conr2286/PocketFT8Xcvr/Extras/AudioSampleRate_ScreenShot.png

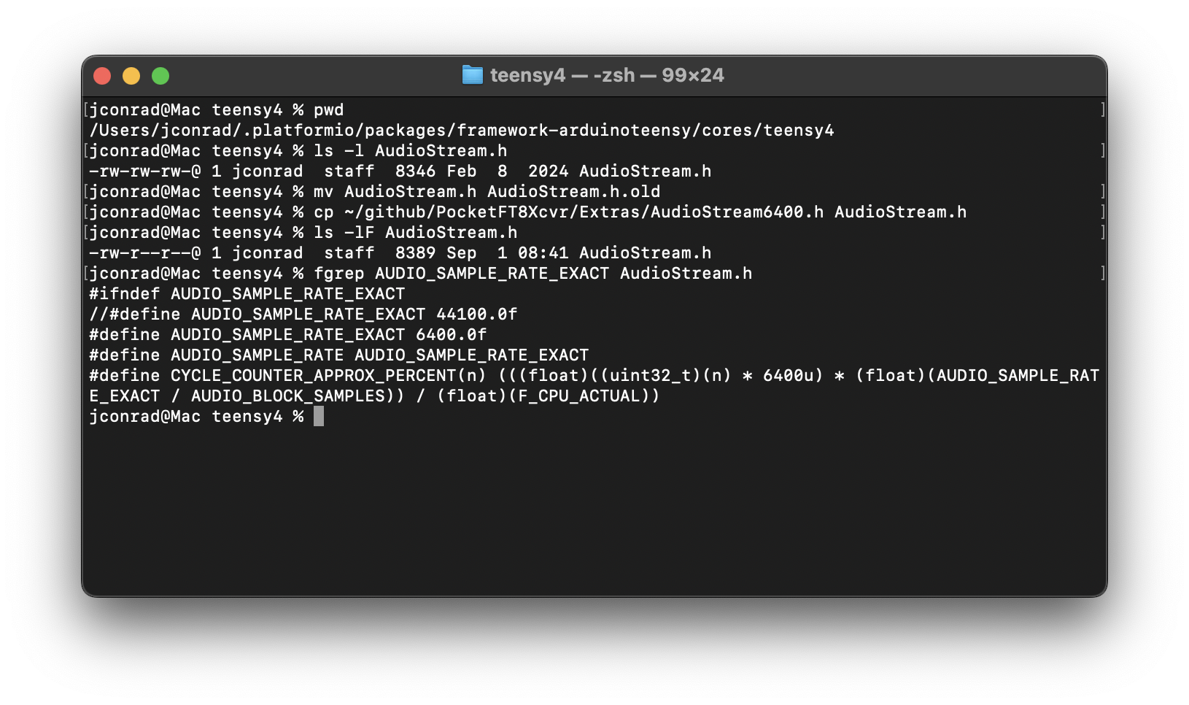
Extras/AudioSampleRate_ScreenShot.png
