conr2286/PocketFT8Xcvr/Investigations/LowPassChebyshev/LowPassFilterNoTrap.png

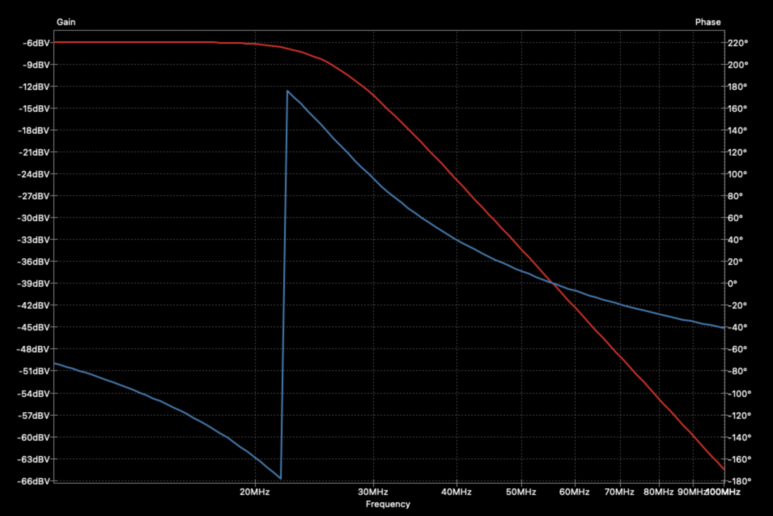
Investigations/LowPassChebyshev/LowPassFilterNoTrap.png
