conr2286/PocketFT8Xcvr/Investigations/LowPassFilter2ndHarmonicTrap/LowPassFilter2ndHarmonicTrap.png

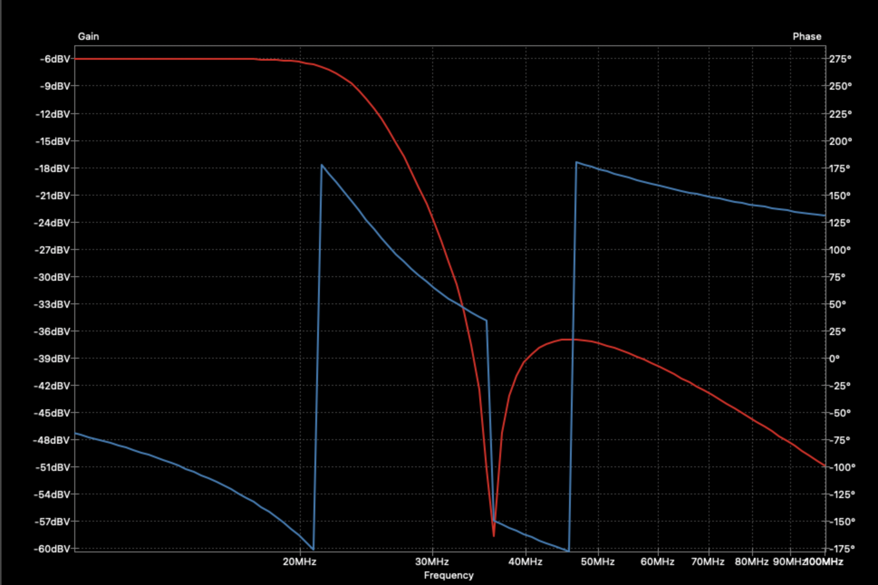
Investigations/LowPassFilter2ndHarmonicTrap/LowPassFilter2ndHarmonicTrap.png
