conr2286/PocketFT8Xcvr/RFFilters/5Pole40MLPFilter/40MLP5PoleSimulation.png

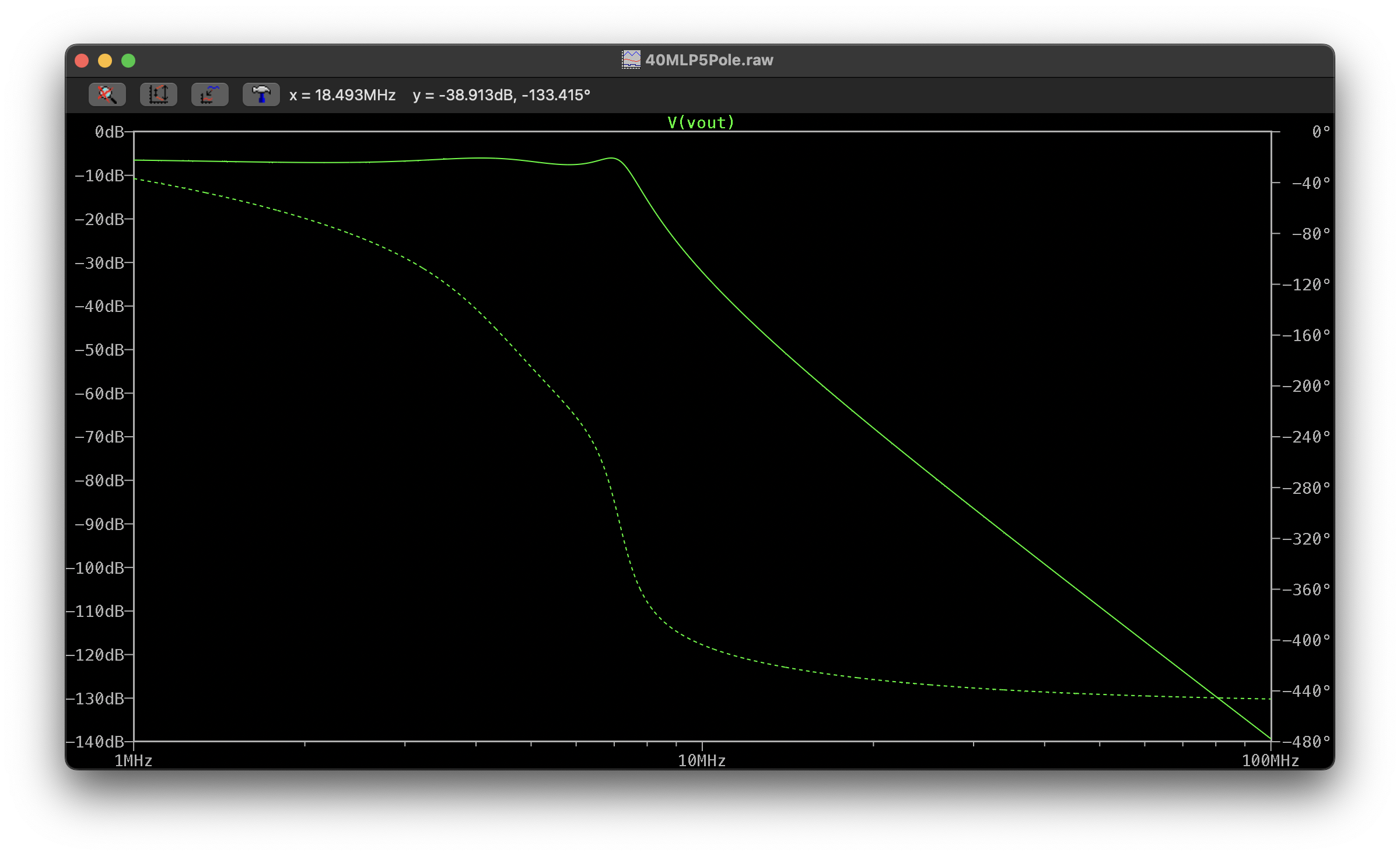
RFFilters/5Pole40MLPFilter/40MLP5PoleSimulation.png
