conr2286/PocketFT8Xcvr/RFFilters/FilterInvestigations/40MLP5Pole.png

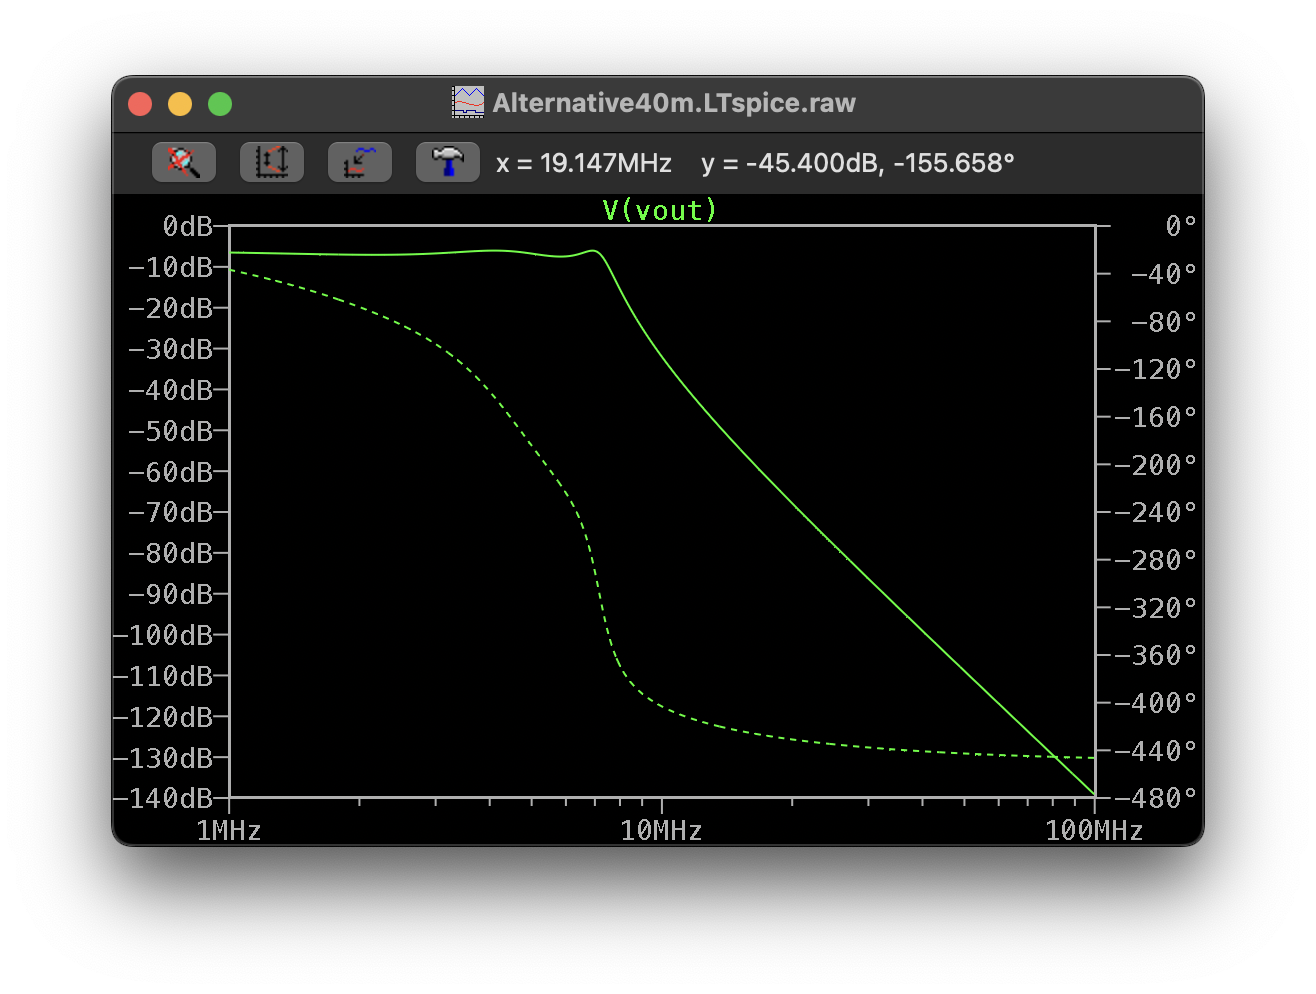
RFFilters/FilterInvestigations/40MLP5Pole.png
