conr2286/PocketFT8Xcvr/SpectralPurity/NarrowView.bmp

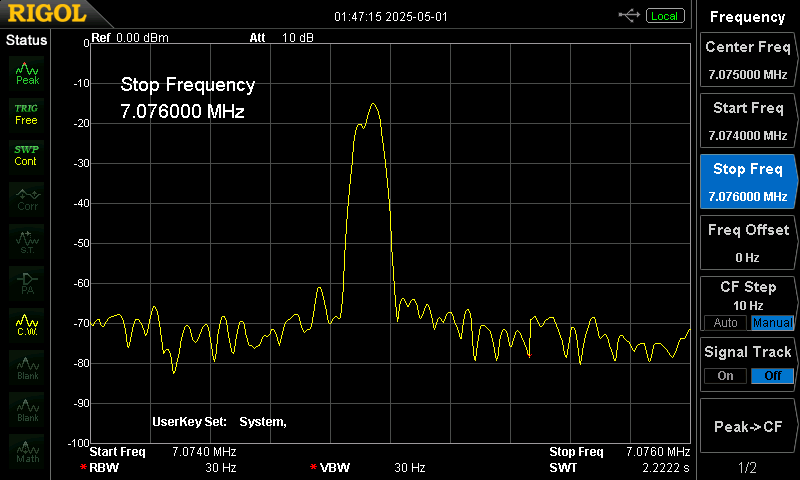
SpectralPurity/NarrowView.bmp
