conr2286/PocketFT8Xcvr/SpectralPurity/TuningCarrier.bmp

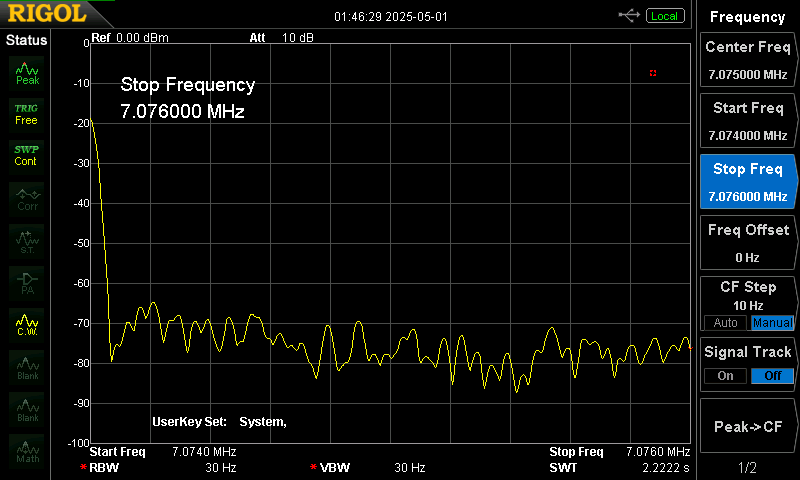
SpectralPurity/TuningCarrier.bmp
