conr2286/PocketFT8Xcvr/RFFilters/FilterInvestigations/40MLP5Pole.asc

C1: cap; 1000pF
C2: cap; 1.3nf
C3: cap; 1000pF
L1: ind; 1.198µH
L2: ind; 1.198µH
R1: res; 50
V1: voltage; SINE(); AC 1; Rser=50
Named nets: Vout, 0, Vin
.ac dec 1000 1meg 100meg
