conr2286/PocketFT8Xcvr/RFFilters/FilterInvestigations/5MhzBandpass.asc

C1: cap; 1.27nf
C2: cap; 1.27nf
C3: Cap; 132pf
L1: ind; 8µh
R1: res; 50
V1: voltage; SINE(); AC 1; Rser=50
Named nets: Vout, 0, Vin
.ac dec 1000 1meg 100meg
