conr2286/PocketFT8Xcvr/PocketFT8XcvrFW/src/Sequencer.cpp

/**
 * SYNOPSIS
 *  Sequencer --- (AKA "RoboOp") Implements a state machine for automated sequencing of FT8 QSOs
 *
 * 42  !!!DON'T PANIC!!!  42
 *  Following the progress of a large state machine like this is challenging.
 *  While the complete FT8 implementation accommodates arcane corner cases to
 *  handle unexpected, exceptional events, the main flow is really not so bad.
 *  Here's the flow for how the RoboOp sequences a QSO begun with our CQ:
 *
 *  Timeslot  CurrentState  Event           Action              NextState   Commentary
 *    0       IDLE          timeslotEvent   N/A                 IDLE        We are monitoring FT8 traffic
 *    0       IDLE          cqButtonEvent   Prepare CQ msg      CQ_PENDING  Operator pressed CQ button, wait for timeslot
 *    1       CQ_PENDING    timeslotEvent   actionPendXmit                  Start transmitting CQ
 *    1       XMIT_CQ       timeslotEvent   N/A                 LISTEN_LOC  Finished sending CQ, start listening for replies
 *    2       LISTEN_LOC    locatorEvent    Prepare RSL msg     RSL_PENDING Received their grid locator
 *    2       RSL_PENDING   timeslotEvent   actionPendXmit                  Start transmitting RSL to remote
 *    3       XMIT_RSL      timeslotEvent   N/A                 LISTEN_RRSL Now listen for our RRSL
 *    3       LISTEN_RRSL   rslMsgEvent     Prepare RRR msg     RRR_PENDING Received our RRSL
 *    4       RRR_PENDING   timeslotEvent   actionPendXmit                  Start transmitting RRR msg
 *    4       XMIT_RRR      timeslotEvent   N/A                 LISTEN_73   Now listen for 73
 *    5       LISTEN_73     eotMsgNoReplyEvent N/A              IDLE        Received 73:  QSO finished normally
 *
 *  See... that wasn't so bad.  The devil is in the details... like what happens if we
 *  receive a completely unexpected msg from the remote station, or they retransmit a
 *  msg we though we already received, or we timeout while attempting to re-re-re-transmit
 *  something to the remote station.  Most of this code is about the devil in the details.
 *
 *  Many events arise from three sources:  timeslot events, GUI buttons,
 *  and received messages.  For many, Sequencer undertakes an action:
 *  prepare a message to [re]transmit in an appropriate timeslot, listen for the remote
 *  station to respond to us, or start the transmitter (in this the appropriate timeslot).
 *  The reference [1] below provides more information about sequencing an FT8 QSO.
 *
 *  Timer events, not to be confused with FT8 timeslot events, often deal with the nasty
 *  business of a QSO gone bad.  This can arise due to QSB, QRM, QLF or even QRT.
 *  Our typical response is to abort the QSO (they aren't responding, at least not as
 *  we expect), or return to an IDLE state to monitor the traffic.
 *
 *  All FT8 messages, received and transmitted, worldwide, start on 15-second
 *  timeslot intervals.  The intervals begin precisely at 0, 15, 30 and 45 seconds
 *  past a minute boundary.  Each message is of a fixed bit length, and requires
 *  12.6 seconds to transmit, the remaining dwell time is available for decoding
 *  messages and preparing a response, if any.  Consider what happens in the
 *  following sequence adopted from [1] below (Sequencer's state, event and action
 *  names are ommitted to simpify the discussion about timeslots):
 *
 *  Timeslot  Destn Source  Content Commentary
 *     0      CQ    K1JT    FN20    K1JT transmits CQ
 *     1                            K1JT listens but hears no response
 *     2      CQ    K1JT    FN20    K1JT retransmits CQ
 *     3                            K1JT again hears no response
 *     4      CQ    K1JT    FN20    Retransmit CQ
 *     5      K1JT  K9AN    EN50    K9AN responds to K1JT with their grid square locator
 *     6      K9AN  K1JT    -10     K1JT sends K9AN's signal report (dB)
 *     7      K1JT  K9AN    R-12    K9AN rogers the report and transmits K1JT's report
 *     8      K9AN  K1JT    RRR     K9AN rogers the received report
 *     9      K1JT  K9AN    73      Traditional QSO ending
 *
 *  K1JT is [re]transmitting CQ during even-numbered timeslots and listening for responses
 *  in odd-numbered timeslots.  K9AN replies during an odd-numbered timeslot to avoid
 *  "doubling" with K1JT's transmissions.  If K9AN initially decodes K1JT's CQ during
 *  timeslot 4, they had 2.4 seconds, at most(!), to choose to respond in the following
 *  timeslot (5).  If they procrastinated, then K9AN's response would necessarily
 *  have to wait for the next odd numbered timeslot (7) as K1JT will likely retransmit CQ
 *  during timeslot 7.
 *
 *  Proper sequencing is important, and is most effectively automated due to the short
 *  dwell time available between when a message is decoded, displayed and the following
 *  timeslot begins.  Human operators simply can't prepare a message in time to send
 *  in that next timeslot --- that's why we have RoboOp (if you've ever worked a CW
 *  contest at 02:00 local time then you know the job).  Now consider the following in
 *  which K1JT's response is lost in the ozone:
 *
 *  Timeslot Destn Source  Content Commentary
 *     0      CQ    K1JT    FN20    K1JT transmits CQ
 *     1      K1JT  K9AN    EN50    K9AN responds to K1JT with their grid square locator
 *     2      K9AN  K1JT    -20     K9AN listens but K1JT's transmission is lost in noise
 *     3      K1JT  K9AN    EN50    K9AN retransmits their grid square locator
 *     4      K9AN  K1JT    -20     K1JT retransmits the lost signal report
 *     5      K1JT  K9AN    R-12    K9AN rogers the received report and transmits K1JT's report
 *     6      K9AN  K1JT    RRR     K9AN rogers the received report
 *     7      K1JT  K9AN    73      Traditional QSO ending
 *
 *  In the above, having heard nothing in timeslot 2, K9AN retransmits their grid square in
 *  timeslot 3 (when K1JT should be listening) in hope of recovering the QSO.  After
 *  successfully receiving K9AN's retransmission in timeslot 3, K1JT retransmits the
 *  signal report lost in timeslot 2.  In general, if nothing is heard when listening
 *  for a remote station to respond to our previous transmission, we retransmit the
 *  previous message.
 *
 *  For the purpose of logging, Sequencer considers a QSO successfully completed when it
 *  receives any form of end-of-transmission (EOT), e.g. RRR, RR73, or 73, from the
 *  remote station ("It aint over till it's over").  Note this is a bit different from
 *  some contests and/or special events --- we're a bit conservative here.
 *
 *  Unexpected FT8 messages, those deviating from the so-called "standard" QSO sequence
 *  described in [1], present Sequencer with a quandry re. what to do as the documented
 *  protocol doesn't really prescribe what to do (i.e. when compared to, say, the TCP
 *  RFCs:).  The easiest thing to do would likely be abandon the QSO, but
 *  Sequencer attempts to get things back on track below.  It's confusing, and much of
 *  the code below addresses the arcane situations when the QSO flows abnormally.
 *
 * DESIGN
 *  Sequencer implements a state machine, driven by event notification methods,
 *  and responds by invoking action methods.  There are two "main" forms of events,
 *  timeslots and received messages.  Others (e.g. Timers) deal with oddities.
 *  RoboOp is a lot of code, but it attempts to behave as would a (very fast) human
 *  operator.
 *
 *  Sequencer expects to be notified about received messages in the timeslot in which they
 *  are decoded (so it can prepare a response to transmit in the following timeslot).
 *  If this doesn't happen for some reason, sequencer is aware of even/odd timeslots and
 *  will pend its response until a suitable timeslot when the remote station should be
 *  listening.  The QSO will really foul up beyond all recognition (FUBAR) if the
 *  remote station changes their even/odd timeslot for transmissions.
 *
 *  Sequencer employs a timer to recognize QSO wreckage (changing band conditions,
 *  remote station QRT, whatever) and abort its automated activities.
 *
 * NOMENCLATURE
 *  "Events" refer to things (e.g. received messages, timeslot boundaries, menu
 *  buttons, timers...) that trigger the state machine.
 *  "Actions" refer to the activities undertaken by the state machine in response to
 *  events.
 *
 * REFERENCES
 *  1. Franke, Somerville and Taylor.  "The FT4 and FT8 Communication Protocols."
 *  QEX.  July/August 2020.
 *
 **/
#include "Sequencer.h"

#include <Arduino.h>
#include <string.h>

#include "Config.h"
#include "DEBUG.h"
#include "LogFactory.h"
#include "PocketFT8Xcvr.h"
#include "SequencerStates.h"
#include "UserInterface.h"
#include "button.h"
#include "decode_ft8.h"
#include "gen_ft8.h"
#include "msgTypes.h"
#include "traffic_manager.h"
#include "UserInterface.h"
#include "Process_DSP.h"
#include "ft8LibIfce.h"

// Many externals in the legacy C code.  TODO:  See if we can simplify these externals.
extern int Transmit_Armned;  // (Maybe) Transmit message pending in next timeslot
extern int xmit_flag;        // Transmitting modulated symbols
extern char Target_Call[];   // Displayed station's callsign
extern int Target_RSL;       // Remote station's RSL

extern int auto_flag;
extern void display_value(int x, int y, int value);
int target_frequency;
// extern uint16_t cursor_line;

void set_Target_Frequency(int cursorFreq);

static UserInterface& ui = UserInterface::getInstance();
static Station& thisStation = Station::getInstance();

// Helper functions

// Our statics
static bool autoReplyToCQ;  // RoboOp automatically transmits reply to CQ

// Macro used to determine if a timeslot sequence number is odd (1) or even (0)
// The macro evaluates to 1 if the argument is odd, else 0 if even.
#define ODD(n) (n % 2)

/**
 * @brief [Re]Initialize the sequencer
 * @param timeoutSeconds #seconds Sequencer will retransmit msg without a response
 * @param logFileName Name of the ADIF logfile
 *
 *  The sequencer notes which timeslot, even or odd-numbered, in which a remote station
 *  is transmitting and attempts to avoid "doubling" with it.  This method resets the
 *  timeslot counter.
 *
 * The timeout parameter governs how long the Sequencer retransmits a message
 * (including CQ) without receiving a response from a remote station.
 *
 *  This method should be invoked once, probably by setup()
 *
 **/
void Sequencer::begin(unsigned timeoutSeconds, const char* logfileName) {
    DTRACE();
    sequenceNumber = 0;                                                      // Reset timeslot counter
    state = IDLE;                                                            // Reset state to idle
    timeoutTimer = Timer::buildTimer(timeoutSeconds * 1000L, onTimerEvent);  // Build the QSO/tuning timeout-timer
    contactLog = LogFactory::buildADIFlog(logfileName);
    // contactLog = LogFactory::buildCSVlog(logfileName);
    setAutoReplyToCQ(false);                          // Disable auto reply to CQ and clear button
    ui.setXmitRecvIndicator(INDICATOR_ICON_RECEIVE);  // Display RECEIVE icon
    lastReceivedMsg = String("");                     // We haven't received anything yet
}  // begin()

/**
 *  Timeslot event
 *
 *  @param sequenceNumber This timeslot's sequence number
 *
 *  A "timeslot" refers to the 15 second FT8 intervals beginning at 0, 15, 30 and 45
 *  seconds past the minute.
 *
 *  loop() notifies this event handler when a new timeslot begins.
 *  Sequencer uses the timeslot's sequenceNumber to determine whether
 *  transmissions to a remote station should occur in even or odd numbered timeslots,
 *  an important consideration ensuring our transmissions do not "double" with those
 *  of a remote station.
 *
 **/
void Sequencer::timeslotEvent() {
    DPRINTF("%s sequenceNumber=%lu, state=%u\n", __FUNCTION__, sequenceNumber, state);

    // Review and purge ancient messages from UI (this is how we dispose of old messages)
    ui.theQSOMsgs->reviewTimeStamps();      // Messages sent to our station
    ui.allDecodedMsgs->reviewTimeStamps();  // All decoded messages

    // Sequencer state determines what action to take
    switch (state) {
        // We are idle, monitoring the traffic --- there's nothing for Sequencer machine to do
        // Or TUNING in which case we also do nothing (Timer will eventually stop run-on Tuning)
        case TUNING:
        case IDLE:
            // DTRACE();
            break;

        // We are awaiting any timeslot to transmit our CQ message.  To do this, we request
        // actionPendXmit() start the transmitter in the forthcoming timeslot.
        case CQ_PENDING:
            DTRACE();
            actionPendXmit(ODD(sequenceNumber), XMIT_CQ);  // Start transmiting CQ in forthcoming timeslot
            break;

        // We are awaiting any timeslot to transmit a "free text" message.  To do this, we request
        // actionPendXmit() start the transmitter in the forthcoming timeslot.
        case MSG_PENDING:
            DTRACE();
            actionPendXmit(ODD(sequenceNumber), XMIT_MSG);  // Start transmitting free text in the forthcoming timeslot
            break;

        // We previously transmitted our CQ message and it is now time to listen
        // for replies.  The loop() modulator already stopped transmitting symbols
        // and switched us to receive mode.  We expect the remote station will
        // transmit their locator msg (e.g. KQ7B W1AW FN31) to us.
        case XMIT_CQ:
            DTRACE();
            state = LISTEN_LOC;  // We are now listening for a locator response to our CQ
            break;

        // We have finished transmitting a free text message.  No further transmission
        // nor response is expected.  Free text messages are not part of the standardized
        // FT8 QSO.
        case XMIT_MSG:
            DTRACE();
            state = IDLE;    // No further transmission nor response expected
            ui.b4->reset();  // Reset the highlighted GUI M* buttons
            ui.b5->reset();
            ui.b6->reset();
            break;

        // In the previous timeslot, we listened for a locator response to our previous
        // CQ but heard nothing.  So... in the next timeslot, we'll retransmit our CQ.
        case LISTEN_LOC:
            DTRACE();
            actionPendXmit(ODD(sequenceNumber), XMIT_CQ);  // Arm transmitter now if needed in next timeslot
            break;

        // We have heard a Tx1 (Locator) response to our CQ, prepared an RSL reply message, and
        // will transmit our RSL in the next appropriate timeslot.
        // Note:  contact records whether the responder transmits in an even or odd timeslot.  Sadly,
        // at least for now, we assume they will *remain* in that even/odd timeslot.  The
        // sequenceNumber variable indicates the previous timeslot's sequence number, not that
        // about to begin (we increment timeslot below).  So... if the currentSequence number
        // is even and the remote station transmits in even, then we will transmit in the next
        // (odd, the one about-to-start) timeslot when our remote station should be listening.
        case RSL_PENDING:
            DTRACE();
            actionPendXmit(contact.oddEven, XMIT_RSL);  // Arm transmitter now if needed in next timeslot
            break;

        // We finished transmission of our RSL reply to their remote station.  Now we expect to
        // hear them send our RRSL signal report to us.  Receiver is already running (loop() turns
        // it on after our last symbol is clocked through the modulator).
        case XMIT_RSL:
            DTRACE();
            state = LISTEN_RRSL;  // We are expecting to receive our signal report from remote station
            break;

        // After transmitting our Tx2 RSL to the remote station, we have not heard a Tx3 RRSL response.
        // We retransmit our RSL when the odd/even timeslot expects the remote to be listening for us.
        case LISTEN_RRSL:
            DTRACE();
            actionPendXmit(contact.oddEven, XMIT_RSL);  // Arm transmitter now if needed in next timeslot
            break;

        // We awaiting an appropriate even/odd timeslot to transmit our prepared Tx4 RRR to remote station
        case RRR_PENDING:
            DTRACE();
            actionPendXmit(contact.oddEven, XMIT_RRR);  // Arm transmitter now if needed in next timeslot
            break;

        // We transmitted our Tx4 RRR to the remote station.  The contact is complete as we expect to receive
        // nothing else but their 73.  We *could* log the contact either here or after we receive their 73.
        // Lets log it later.  Our receiver is already running.
        case XMIT_RRR:
            DTRACE();
            state = LISTEN_73;  // Listen for their 73
            break;

        // We listened for the remote station's 73-type msg but have heard nothing.
        // Let's retransmit an RRSL to tease-out a response from remote and
        // rely on the timer to close the QSO if it's hopeless.  Our state remains
        // unchanged while we continue to listen.
        case LISTEN_73:
        case LISTEN_RRR:
            DTRACE();
            actionPendXmit(contact.oddEven, XMIT_RRSL);  // Retransmit our RRSL to remote
            break;

        // We await contacting a displayed station after our operator clicked on remote's message (i.e. we
        // may have the remote station's locator).  We expect clickDecodedMessageEvent() to have previously
        // initialized the QSO struct and prepared our outbound locator message.
        case LOC_PENDING:
            DTRACE();
            actionPendXmit(contact.oddEven, XMIT_LOC);  // Arm transmitter now if needed in next timeslot
            break;

        // We have transmitted our location to the remote station and await reception of their RSL
        case XMIT_LOC:
            DTRACE();
            state = LISTEN_RSL;  // We will listen for our RSL from the remote station
            break;

        // We listened for remote's RSL message to us but heard nothing.  Retransmit our LOC.
        case LISTEN_RSL:
            DTRACE();
            actionPendXmit(contact.oddEven, XMIT_LOC);  // Arm transmitter now if needed in next timeslot
            break;

        // We are waiting for an appropriate even/odd timeslot to transmit an RRSL message to remote station
        case RRSL_PENDING:
            DTRACE();
            actionPendXmit(contact.oddEven, XMIT_RRSL);  // Arm transmitter now if needed in next timeslot
            break;

        // We have transmitted their RRSL message to the remote station and are now receiving their response
        case XMIT_RRSL:
            DTRACE();
            state = LISTEN_RRR;  // We expect an RRR or RR73
            break;

        // We are waiting for an appropriate even/odd timeslot to transmit a 73 message to remote station
        case M73_PENDING:
            DTRACE();
            actionPendXmit(contact.oddEven, XMIT_73);  // Arm transmitter now if needed in next timeslot
            break;

        // We have transmitted the 73 message to the remote station.  Another QSO in the bag. :)
        case XMIT_73:
            DTRACE();
            endQSO();
            state = IDLE;  // We have finished
            break;

        // Unexpected state !?
        default:
            DPRINTF("Unexpected Sequencer state =%u\n", state);
            break;
    }

    // Increment sequenceNumber to begin the next timeslot
    sequenceNumber++;

}  // timeSlotEvent()

/**
 *  Received message event
 *
 *  @param msg Reference to the decoded message
 *
 *  The receiver notifies this event handler when it has successfully decoded a message:
 *    msg->field1   Destination station (may be our station, another station, CQ, or QRZ)
 *    msg->field2   Source station (transmitting the message)
 *    msg->field3   Conveyed content
 *    msg->msgType  Defines what to expect in field3 (e.g. LOC, RSL, 73...)
 *
 *  Received messages, incoming from decode_ft8(), are too broad in scope for us to
 *  act upon until we analyze their type and trigger the appropriate event for that msgType
 *  in our current state.
 *
 *  We employ a timeout Timer to abort a run-on QSO during difficult (QRM, QRN, QSB, QLF...)
 *  conditions.  In general (see exceptions below), we restart Timer when we receive a
 *  message from the remote station.  This means the Timer aborts a run-on QSO only after
 *  we don't hear anything from the remote for a "long" time.  There is some risk with this
 *  approach:  if a QLF remote repeatedly retransmits the same FT8 message "forever"
 *  then we will continue to respond even though the QSO doesn't really make any real
 *  progress.  If this proves problematic, we should use a 2nd Timer to kill a stuck QSO.
 *
 **/
void Sequencer::receivedMsgEvent(Decode* msg) {
    // Sadly, some FT8 encoders apparently transmit "RR73" as a locator rather than as an EOT
    // (KQ7B thought this wasn't supposed to happen but we've seen it).  We work around this
    // by assuming RR73 means end-of-transmission, not somewhere in the North Sea.
    if (msg->msgType == MSG_LOC && strstr(msg->field3, "RR73")) msg->msgType = MSG_RR73;

    // When debugging, print some things from the received message
    DPRINTF("%s %s %s %s msgType=%u, sequenceNumber=%lu state=%u\n", __FUNCTION__, msg->field1, msg->field2, msg->field3, msg->msgType, sequenceNumber, state);

    // Remove angle brackets in-place from field1 and field2 callsigns (if present)
    trimBracketsFromCallsign(msg->field1);
    trimBracketsFromCallsign(msg->field2);

    // Build a String of the received message fields for us to display
    static const String sp(" ");
    String thisReceivedMsg = String(msg->field1) + sp + String(msg->field2) + sp + String(msg->field3);

    // The Sequencer analyzes mesages of interest to our station
    if (isMsgForUs(msg)) {
        DPRINTF("this msg is for us:  '%s' '%s' '%s'\n", msg->field1, msg->field2, msg->field3);

        // Display messages sent directly to us (not a CQ) in StationMsgs
        if (msg->msgType != MSG_CQ) {
            // Display messages addressed to us in our Station Messages box.  Retransmissions appear
            // in yellow rather than wasting another line in our little Station Messages GUI box
            if (thisReceivedMsg == lastReceivedMsg) {
                lastStationMsgsItem = ui.theQSOMsgs->addStationMessageItem(ui.theQSOMsgs, thisReceivedMsg, QSO_MSG_RECVRPT);  // Repeated (retransmission from remote station) message
            } else {
                lastStationMsgsItem = ui.theQSOMsgs->addStationMessageItem(ui.theQSOMsgs, thisReceivedMsg, QSO_MSG_RECVD);  // New received msg
            }
            lastReceivedMsg = thisReceivedMsg;  // Remember this received msg text for when the next msg arrives
        }

        // What type of FT8 message did we receive?  ToDo:  Need to handle received FT8 free text message somehow somewhere.
        switch (msg->msgType) {
            // Did we receive a station's Tx6 CQ?
            case MSG_CQ:
                // DTRACE();
                cqMsgEvent(msg);  // Yes, we heard someone's CQ
                break;

            // Did we receive their Tx1 locator message?
            case MSG_LOC:
                // DTRACE();
                startTimer();       // Keep this QSO alive as long as remote station is responding
                locatorEvent(msg);  // They are responding to us with a locator
                break;

            // Did we receive an [R]RSL containing our signal report?
            case MSG_RSL:
            case MSG_RRSL:
                // DTRACE();
                startTimer();      // Keep this QSO alive while remote station continues to respond
                rslMsgEvent(msg);  // They sent our signal report
                break;

            // Did we receive their EOT that does not expect a reply?  We don't restart the Timer for EOT.  Let 'er die.
            case MSG_73:
                // DTRACE();
                eotMsgNoReplyEvent(msg);  // No reply to 73 msg.
                break;

            // Did we receive their EOT that expects a reply?  We don't restart the Timer for EOT.
            case MSG_RR73:
            case MSG_RRR:
                // DTRACE();
                eotMsgReplyEvent(msg);  // We reply to RR73/RRR msg
                break;

            // The Sequencer does not currently process certain message types.  We don't restart the Timer for unsupported msgs.
            // case MSG_BLANK:
            case MSG_FREE:  // TODO:  we should try to handle this one someday somewhere.
            case MSG_TELE:
            case MSG_UNKNOWN:
            default:
                DPRINTF("***** ERROR:  Unsupported received msgType=%d\n", msg->msgType);
                break;
        }  // switch
    }
    // DTRACE();

}  // receivedMsgEvent()

/**
 * @brief Process received CQ message event
 *
 * If the operator has enabled automatic responses with the Tx button, the Sequencer ("RoboOp") automatically
 * responds to the first received CQ if we aren't already engaged in another activity (e.g. calling CQ ourself
 * or in an unfinished QSO).  EXCEPT:  By default, RoboOp ignores duplicate entries from the log.
 *
 * You may question why we need RoboOp.  Between the receipt of a CQ and the first opportunity to respond is
 * the FT8 "dwell" time of <= 2.6 seconds.  If we miss that timeslot opportunity, then we have to
 * sit out yet another timeslot (30 seconds so far) before the next chance to reply without doubling with the
 * remote station's CQ transmissions.  Thus, without RoboOp, we have only 2.6 secondes (at most) to
 * respond if we wish to avoid the 30 second penalty.  RoboOp is faster than a 70-yo CW operator at the
 * low end of 20 meters.  ;)
 */
void Sequencer::cqMsgEvent(Decode* msg) {
    // Has the operateR enabled RoboOp's automatic replies with the Tx button?
    if (!autoReplyToCQ) return;  // No... nothing to do here

    // Avoid responding to previously logged duplicates unless enabled by CONFIG.JSON
    String dupMsg;
    if (config.enableDuplicates) {
        dupMsg = String("Reply to ") + String(msg->field2);
        ui.applicationMsgs->setText(dupMsg.c_str());
    } else if (ContactLogFile::isKnownCallsign(msg->field2)) {
        dupMsg = String("Ignoring ") + String(msg->field2);
        ui.applicationMsgs->setText(dupMsg.c_str());
        return;  // RoboOp ignores stations already in the log
    }

    // Automatically respond to received CQ message if we are not already engaged in a QSO
    switch (state) {
        case IDLE:
            DTRACE();
            startQSO(msg->field2, ODD(msg->sequenceNumber));
            contact.setWorkedLocator(msg->field3);  // Record their locator if we recvd it
            setXmitParams(msg->field2, msg->snr);   // Inform gen_ft8 of remote station's info
            DPRINTF("Target_Call='%s', msg.field2='%s', msg.rsl=%d, Target_RSL=%d msg.sequenceNumber=%lu, contact.oddEven=%u\n", Target_Call, msg->field2, msg->snr, Target_RSL, msg->sequenceNumber, contact.oddEven);
            set_message(MSG_LOC);  // We get QSO underway by sending our locator
            startTimer();          // Start the Timer to terminate a run-on QSO
            state = LOC_PENDING;   // Await appropriate timeslot to transmit to Target_Call
            target_frequency = msg->freq_hz;
            display_value(270, 258, target_frequency);  // TODO:  Should this be a ui method?
            set_Target_Frequency(target_frequency);
            break;

        // Automatic responses are disabled if we are calling CQ or otherwise engaged
        default:
            DTRACE();
            break;

    }  // switch
}  // cqMsgEvent()

/**
 * @brief Operator clicked the TUNE button.
 *
 */
void Sequencer::tuneButtonEvent() {
    // DTRACE();

    switch (state) {
        // Stop TUNING in-progress (toggle)
        case TUNING:
            tune_Off_sequence();
            ui.b2->reset();
            stopTimer();
            state = IDLE;
            // DTRACE();
            break;

        // Ignore the TUNE button if we busy doing something else.  Our operator likely has thick fingers.
        case XMIT_RSL:
        case XMIT_CQ:
        case XMIT_LOC:
        case XMIT_RRR:
        case XMIT_RRSL:
        case XMIT_73:
            break;

        // Start TUNING (transmit a dead carrier)
        case IDLE:
        default:
            // DTRACE();
            //  Stop anything underway
            terminate_transmit_armed();
            xmit_flag = 0;  // Stop modulation in loop()

            // Transmit a dead, unmodulated carrier
            tune_On_sequence();
            state = TUNING;
            // ui.applicationMsgs->setText("TUNING");

            // Start a Timer to terminate TUNING in case our operator forgets to toggle the Tune button
            // DTRACE();
            startTimer();
            break;
    }

}  // tuneButtonEvent();

/**
 * @brief Our operator clicked one of the transmit free text buttons (M0, M1 or M2)
 * @param msg The possibly empty free text msg to transmit
 *
 */
void Sequencer::msgButtonEvent(char* msg) {
    DTRACE();

    // Ignore nonsense
    if ((msg == NULL) || (strlen(msg) == 0)) return;

    // The required action depends upon which state the Sequencer resides
    switch (state) {
        // We can send a free text message if we are not already engaged in a QSO
        case IDLE:
            // Encode the free text message for transmission by the FSK modulator
            set_message(msg);  // Build the FT8 FSK tone array

            // Prepare the sequencer to transmit the free text message
            state = MSG_PENDING;                              // Await the next timeslot
            startTimer();                                     // Start the Timer to terminate run-on transmissions
            ui.setXmitRecvIndicator(INDICATOR_ICON_PENDING);  // Tell operator msg is pending
            break;

        // The M* buttons are ignored when we are in the midst of an existing QSO.
        default:
            DTRACE();

    }  // switch

}  // msgButtonEvent()

/**
 *  @brief Our operator clicked the CQ button
 *
 **/
void Sequencer::cqButtonEvent() {
    DTRACE();

    // The required action depends upon which state the Sequencer machine currently resides
    switch (state) {
        // Prepare to transmit CQ in the next available timeslot.  Since we are not interacting with
        // another station, we are not concerned about doubling with them, so we can transmit in the
        // very next timeslot.
        case IDLE:         // We are currently idle
        case LOC_PENDING:  // Operator decided to CQ rather than respond to a known station

            // Disable RoboOp's autoreply to CQ.  Our decision to transmit our own CQ overides
            // responding to received CQ messages.
            setAutoReplyToCQ(false);

            // Prepare to call CQ
            set_message(MSG_CQ);                              // Build our CQ message tones and display message text
            state = CQ_PENDING;                               // Await the next timeslot
            startTimer();                                     // Start the Timer to terminate run-on CQ transmissions
            ui.setXmitRecvIndicator(INDICATOR_ICON_PENDING);  // Notify operator of pending transmission
            break;

        // Our operator toggled the CQ button to stop a pending or in-progress CQ transmission.
        case CQ_PENDING:  // Pending timeslot to transmit CQ
        case XMIT_CQ:     // CQ transmission in progress
        case LISTEN_LOC:  // Listening for a response to our CQ message[s]
            DTRACE();
            state = IDLE;                                     // Return to idle
            xmit_flag = 0;                                    // Stop the modulator
            terminate_transmit_armed();                       // Disarm the transmitter
            clearOutboundMessageDisplay();                    // Clears displayed outbound message as we're now idle
            stopTimer();                                      // Stop the Timer
            ui.b0->reset();                                   // Reset highlighted button
            ui.setXmitRecvIndicator(INDICATOR_ICON_RECEIVE);  // Let operator know the receiver is running
            break;

            // The CQ button is ignored during most states
        default:
            DTRACE();
            break;
    }
}

/**
 *  Our operator clicked a decoded message to initiate a QSO
 *
 *  These overloaded event handlers initiate a QSO by contacting a displayed, received message.
 *
 *  Note the overloaded function can be called with either a msgIndex or with a pointer
 *  to a decoded msg.
 *
 *  We create a QSO contact here, perhaps prematurely (Target_Call may not reply),
 *  because we need an even/odd timeslot record of when Target_Call is transmitting.
 *  Also... this may be the only time when we'll have Target_Call's locator.
 *
 **/
void Sequencer::clickDecodedMessageEvent(unsigned msgIndex) {
    // Find the decoded message as we need some info from it
    Decode* msg = getDecodedMsg(msgIndex);
    clickDecodedMessageEvent(msg);
}  // clickDecodedMessageEvent()

void Sequencer::clickDecodedMessageEvent(Decode* msg) {
    // Assert Target_Call==msg->field2 as this stuff could become FUBAR
    DFPRINTF("sequenceNumber=%lu, Target_Call='%s', msg->field2='%s', msg->sequenceNumber=%u, state=%u\n", sequenceNumber, Target_Call, msg->field2, msg->sequenceNumber, state);
    Sequencer& theSequencer = Sequencer::getSequencer();

    // Sanity check
    if (msg != NULL) {
        // We can only contact msgTypes known to include a usable callsign for the remote station
        switch (msg->msgType) {
            // We cannot respond to these FT8 message types
            // case MSG_BLANK:    // Hashed (unusable) callsign (sorry)
            case MSG_FREE:     // Free text (no callsign in free text messages)
            case MSG_TELE:     // Telemetry
            case MSG_UNKNOWN:  //
            default:           //"...lost in the ozone again."
                DPRINTF("Cannot respond to msgType %d\n", msg->msgType);
                return;  // Ignore operator's selection
                break;

            // We can respond to these FT8 message types
            case MSG_CQ:    // Normal response to remote's CQ
            case MSG_LOC:   // Early Tail-ending
            case MSG_RSL:   // Early Tail-ending
            case MSG_RRSL:  // Early Tail-ending
            case MSG_RR73:  // Tail-ending
            case MSG_RRR:   // Tail-ending
            case MSG_73:    // Tail-ending
                break;
        }  // msgType

        // Cleanup current activity
        if (state == TUNING) tune_Off_sequence();     // Stop tuning
        receive_sequence();                           // Stop the transmitter
        theSequencer.highlightAbortedTransmission();  // Let operator know we aborted something in progress
        theSequencer.endQSO();                        // This QSO, if any, is finished
        clearOutboundMessageText();                   // Clear outbound message text chars

        // Start a QSO contact for the remote station
        startQSO(msg->field2, ODD(msg->sequenceNumber));
        contact.setWorkedLocator(msg->field3);  // Record their locator if we have it
        setXmitParams(msg->field2, msg->snr);   // Inform gen_ft8 of remote station's info
        DPRINTF("Target_Call='%s', msg.field2='%s', msg.rsl=%d, Target_RSL=%d msg.sequenceNumber=%lu, contact.oddEven=%u\n", Target_Call, msg->field2, msg->snr, Target_RSL, msg->sequenceNumber, contact.oddEven);
        set_message(MSG_LOC);  // Build tones for modulator to transmit our locator
        startTimer();          // Start the Timer to terminate a run-on QSO
        ui.b0->reset();        // Reset highlighted button
        state = LOC_PENDING;   // We are awaiting a timeslot to transmit our locator

    }  // sanity

}  // clickDecodedMessageEvent()

/**
 * @brief Static callback function notified if/when the timeout Timer expires
 * @param thisTimer Pointer to the expiring Timer (not actually used)
 *
 * The timeout Timer limits the duration of a run-on QSO or TUNING activity.
 * The Timer was created by begin(), started at the beginning of a QSO/TUNE
 * activity, and is normally stopped when that QSO/TUNE completes normally.
 * The duration was established by begin() and configurable in CONFIG.JSON.
 *
 * NOTE:  Timer events are synchronous, not asynchronous, (we don't have to worry
 * about them interrupting us doing something else --- there are no critical
 * section worries here).
 */
void Sequencer::onTimerEvent(Timer* thisTimer) {
    // Because onTimerEvent() is static, we have to find the Sequencer singleton object as we have no this pointer
    Sequencer& theSequencer = Sequencer::getSequencer();
    DFPRINTF("sequenceNumber=%lu, state=%u\n", theSequencer.sequenceNumber, theSequencer.state);

    // auto_flag enables RoboOp to continue to respond to received CQ messages.  This flag was
    // used during development for debugging.  However, Franke, Somerville and Taylor require
    // "Robotic or unattended QSOs must be explicitly disallowed" and so auto_flag is disabled.
    // For your maximum confusion, RoboOp is not a true robotic/unattended QSO as it merely
    // enables this station to respond to a single CQ:  the operator must restart RoboOp after
    // each QSO attempt.
    // if (auto_flag == 1)
    //     setAutoReplyToCQ(true);
    // else
    //     setAutoReplyToCQ(false);

    // Decide what to do about the time-out
    switch (theSequencer.state) {
        // We don't do anything if we were IDLE.  Not sure why we had a Timer active.
        case IDLE:
            DTRACE();
            break;

        // Interrupt endless TUNING --- if it aint tuned by now, it aint gonna get tuned
        case TUNING:
            tune_Off_sequence();        // Stop the transmitted carrier
            theSequencer.state = IDLE;  // IDLE the state machine
            break;

        // Interrupt current QSO listening for a specific response from the remote station
        case LISTEN_LOC:
        case LISTEN_RRR:
        case LISTEN_RRSL:
        case LISTEN_RSL:
        case LISTEN_73:
            theSequencer.highlightAbortedTransmission();  // Let our operator know we aborted
            theSequencer.endQSO();                        // Misc activities to terminate QSO
            clearOutboundMessageText();                   // Clear outbound message text chars from UI
            theSequencer.state = IDLE;                    // IDLE the state machine.  QSO is over.
            break;

        // Interrupt pending transmission awaiting an appropriate timeslot
        case CQ_PENDING:
        case LOC_PENDING:
        case RRR_PENDING:
        case RSL_PENDING:
        case RRSL_PENDING:
        case M73_PENDING:
            theSequencer.highlightAbortedTransmission();  // Let our operator know we aborted
            theSequencer.endQSO();                        // This QSO is finished
            clearOutboundMessageText();                   // Clear outbound message text chars
            theSequencer.state = IDLE;                    // IDLE the state machine
            break;

        // Interrupt an active transmission (loop() is actively modulating symbols).  We
        // actually stop modulation below this switch.
        case XMIT_LOC:
        case XMIT_RRR:
        case XMIT_RRSL:
        case XMIT_RSL:
        case XMIT_73:
        case XMIT_CQ:
            theSequencer.highlightAbortedTransmission();  // Let our operator know we've aborted
            theSequencer.endQSO();                        // This QSO is finished
            clearOutboundMessageText();                   // Clear outbound message text chars from UI
            theSequencer.state = IDLE;                    // IDLE the state machine
            break;

        // Interrupt a QSO gone bad (e.g. QRN, QRM, QSB, QRT, whatever) --- it's over
        default:
            break;
    }

    // Always reset a few more things
    theSequencer.stopTimer();  // Cancel the QSO Timer

    // Stop modulation, disarm the transmitter, clear the outbound message, and turn the receiver on
    xmit_flag = 0;                  // Stop modulation
    terminate_transmit_armed();     // Dis-arm the transmitter
    clearOutboundMessageDisplay();  // Clear displayed outbound message, if any
    clearOutboundMessageText();     // Clear outbound message text string
    receive_sequence();             // Only need to do this if in-progress transmission aborted

    // Reset highlighted buttons, if any
    ui.b0->reset();  // Reset highlighted button
    ui.b2->reset();  // Reset highlighted button
                     // resetButton(BUTTON_CQ);

}  // onTimerEvent()

/**
 * @brief Operator clicked the ABORT button to halt transmissions
 *
 * For now, we handle this the same as when the QSO timeout Timer expires
 *
 */
void Sequencer::abortButtonEvent() {
    DTRACE();
    setAutoReplyToCQ(false);                          // Disable RoboOp's auto replies
    onTimerEvent(NULL);                               // Pretend the QSO Timer expired (ends QSO if any)
    ui.setXmitRecvIndicator(INDICATOR_ICON_RECEIVE);  // Let operator know receiver is on
}  // abortButtonEvent()

/**
 * We have received our signal report from the remote station
 *
 * @param msg Their decoded RSL message
 *
 **/
void Sequencer::rslMsgEvent(Decode* msg) {
    DPRINTF("state=%d\n", state);
    // Action to be taken depends upon the Sequencer's current state
    switch (state) {
        // Remote station sent RRSL.  We'll send them an RRR to wrap things up.
        case LISTEN_RRSL:
            DTRACE();
            contact.setMyRSL(msg->field3);         // Record our signal report in QSO
            contact.setWorkedRSL(msg->snr);        // Record their RSL at the same time as ours
            setXmitParams(msg->field2, msg->snr);  // Inform gen_ft8 of remote station's info
            set_message(MSG_RRR);                  // Prepare and display an RRR message
            state = RRR_PENDING;                   // We must await an appropriate even/odd timeslot
            ui.setXmitRecvIndicator(INDICATOR_ICON_PENDING);
            break;

        // Remote station sent our RSL and we should respond with their RRSL
        case LISTEN_RSL:
            DTRACE();
            contact.setMyRSL(msg->field3);         // Record our signal report in QSO structure
            contact.setWorkedRSL(msg->snr);        // Record their RSL at the same time as ours
            setXmitParams(msg->field2, msg->snr);  // Inform gen_ft8 of remote station's info
            set_message(MSG_RRSL);                 // Prepare to send their signal report to remote station
            state = RRSL_PENDING;                  // Await an appropriate even/odd timeslot
            ui.setXmitRecvIndicator(INDICATOR_ICON_PENDING);
            break;

        // We were expecting a LOC but received a signal report.  We likely were calling CQ
        // and listening for a response which came with an RSL.  Let's try to cobble-up a
        // QSO from what we've heard.
        case LISTEN_LOC:
            DTRACE();
            startQSO(msg->field2, ODD(msg->sequenceNumber));
            contact.setMyRSL(msg->field3);         // Record our RSL from remote station
            contact.setWorkedRSL(msg->snr);        // Record their RSL at the same time as ours
            setXmitParams(msg->field2, msg->snr);  // Inform gen_ft8 of remote station's info
            DPRINTF("Target_Call='%s', msg.field2='%s', msg.rsl=%d, Target_RSL=%d msg.sequenceNumber=%lu, qso.oddEven=%u\n", Target_Call, msg->field2, msg->snr, Target_RSL, msg->sequenceNumber, contact.oddEven);
            set_message(MSG_RRSL);  // Roger our RSL and send their RSL to remote station
            state = RRSL_PENDING;   // Transmit their RSL in next appropriate timeslot
            break;

        // Ignore non-sense
        default:
            DPRINTF("***** NOTE:  Ignoring received msgType=%d from %s because state=%d\n", msg->msgType, msg->field2, state);
            break;

    }  // switch

}  // rslMsgEvent()

/**
 * @brief Received an EOT message that does not expect a reply from us
 *
 * @note An End-of-Transmission (EOT) is any kind of 73-like message from
 * the remote station indicating we shouldn't expect to receive further
 * messages from them.
 *
 * @param msg Their decoded EOT message
 *
 **/
void Sequencer::eotMsgNoReplyEvent(Decode* msg) {
    // The action taken depends upon our state
    switch (state) {
        // Process a QSO ending more or less normally
        case LISTEN_73:   // We expected their 73
        case LISTEN_RRR:  // We expected an RRR but received a 73 --- I guess it's over
            DTRACE();
            endQSO();
            state = IDLE;  // It's definitely over now
            break;

        // We were trying to get a CQ transmission underway and can ignore this 73 which
        // presumably is left-over from a previous QSO.
        case CQ_PENDING:
        case XMIT_CQ:
        case LISTEN_LOC:
            DTRACE();
            break;

        // We were somewhere in midst of a QSO when the remote station 73'd.  QSO maybe incomplete.
        // TODO:  log???
        default:
            DTRACE();
            endQSO();
            state = IDLE;  // Return to IDLE
            break;
    }

    // This QSO is finished and we no longer need the Timer
    stopTimer();

}  // eotMsgNoReplyEvent()

/**
 * @brief Received an EOT message that expects our 73 reply
 *
 * @param msg Their decoded EOT message
 *
 * @note An End-of-Transmission (EOT) is any kind of 73-like message from
 * the remote station indicating we shouldn't expect to receive further
 * messages from them.  However, their RRR and RR73 messages expect a 73
 * reply from us.
 *
 * We listen either for a 73 or an RRR, never an RR73.  If they send
 * us an RR73 then we treat it like an RRR and transmit a 73 reply.
 *
 **/
void Sequencer::eotMsgReplyEvent(Decode* msg) {
    // The action taken depends upon our state
    switch (state) {
        // Process end of QSO when they expect a 73 reply from us
        case LISTEN_73:   // We expected 73 but they've requested a 73 reply.  Hmm.
        case LISTEN_RRR:  // They expect 73 from us
            DTRACE();
            setXmitParams(msg->field2, msg->snr);  // Inform gen_ft8 of remote station's info
            set_message(MSG_73);                   // Prepare an RRR message
            state = M73_PENDING;                   // We must await an appropriate even/odd timeslot
            ui.setXmitRecvIndicator(INDICATOR_ICON_PENDING);
            // TODO:  qso.end()???
            break;

        // We were trying to get a CQ transmission underway and can ignore the EOT which
        // presumably is left-over from a previous QSO.  Yes, this really happens.
        case CQ_PENDING:
        case XMIT_CQ:
        case LISTEN_LOC:
            DTRACE();
            break;

        // We were somewhere in a QSO when the remote station suddenly 73'd.  QSO maybe incomplete.
        default:
            DTRACE();
            endQSO();
            state = IDLE;  // Return to IDLE
            break;
    }
}

/**
 *  We have received the remote station's locator (i.e. maidenhead grid square)
 *
 *  @param msg Their decoded message
 *
 *  A remote may send us a locator in response to our own CQ or perhaps to
 *  tailend our previous QSO.  Or the locator may be a retransmission arising
 *  after we failed to decode the original.
 *
 *  Upon entry here, sequenceNumber identifies the timeslot when we received
 *  the locator message.  We record whether the remote station
 *  is transmitting in even or odd-numbered timeslots, and prepare an RSL
 *  message to transmit in the next appropriate odd/even timeslot.
 *
 *  RoboOp is currently unable to accommodate remote stations that change their
 *  timeslot odd/even-ness.  After recording what they are doing here, we expect
 *  them to always transmit in the same odd/even timeslots.
 *
 **/
void Sequencer::locatorEvent(Decode* msg) {
    // The action to be taken depends upon the Sequencer's current state
    switch (state) {
        // We have a CQ pending or were listening for a response to our own CQ
        case CQ_PENDING:  // We were going to [re]transmit CQ but received this msg first
        case LISTEN_LOC:  // We were listening for a response to our CQ and received this msg
            DTRACE();
            startQSO(msg->field2, ODD(sequenceNumber));
            // contact.begin(thisStation.getCallsign(), msg->field2, thisStation.getFrequency(), "FT8", thisStation.getRig(), ODD(sequenceNumber), thisStation.getSOTAref());  // Start gathering QSO info
            contact.setWorkedLocator(msg->field3);  // Record responder's locator
            setXmitParams(msg->field2, msg->snr);   // Inform gen_ft8 of remote station's info
            DPRINTF("Target_Call='%s', msg.field2='%s', msg.rsl=%d, Target_RSL=%d msg.sequenceNumber=%lu, qso.oddEven=%u\n", Target_Call, msg->field2, msg->snr, Target_RSL, msg->sequenceNumber, contact.oddEven);
            set_message(MSG_RSL);  // Prepare tones to transmit RSL
            state = RSL_PENDING;   // Must await an appropriate timeslot when the remote station is listening
            // ui.setXmitRecvIndicator(INDICATOR_ICON_PENDING);  // Let operator know we have a transmission pending
            break;

        // Something is wrong and we don't know why we apparently received their locator.  Maybe we should reset everything???
        // NOTE:  We may not be handling tail-enders optimally here.
        default:
            DPRINTF("***** ERROR:  Received unexpected msgType=%d in state %d\n", msg->msgType, state);
            break;

    }  // switch

}  // locatorEvent()

/**
 *  Determine if a received message is of concern to us
 *
 *  @param msg Pointer to the decoded message
 *
 *  @return true if interesting, false if not
 *
 *  Examples of messages that may or may not be of interest to KQ7B:
 *    CQ W1AW EN15          //Interesting
 *    KQ7B W1AW -9          //Interesting
 *    CQ POTA W1AW EN15     //Not interesting (TODO someday???)
 *.   KQ7B/R W1AW EN15      //Interesting
 *    F4CQS KX8XX EN74      //Not interesting
 *.   KQ7BA W1AW EN15       //Not interesting
 *
 **/
bool Sequencer::isMsgForUs(Decode* msg) {
    DPRINTF("isMsgForUs('%s')\n", msg->field1);

    // A received msg is "for us" if our callsign or CQ appears as the destination station's callsign
    bool myCall = strncmp(msg->field1, thisStation.getCallsign(), sizeof(msg->field1)) == 0;  // Sent directly to us?
    bool cq = strcmp(msg->field1, "CQ") == 0;
    bool msgIsForUs = cq || myCall;
    return msgIsForUs;
}

/**
 *  Action routine to begin modulation in the requested odd/even timeslot
 *
 *  @param oddEven begin modulation in 1==odd, 0==even-numbered timeslot
 *  @param newState new state value if transmitter is armed
 *
 *  @note An "action" routine implements a complex response to a
 *  significant Sequencer state machine event
 *
 *  @note We don't actually modulate anything here, all we do is setup the global
 *  flags so loop() will begin transmitting FSK modulated symbol tones.
 *
 *  + You must invoke set_message() to prepare the outbound message tones prior
 *  to invoking actionPendXmit
 *
 *  + Upon entry, sequenceNumber identifies the *current* timeslot,
 *  not the next timeslot.  The oddEven parameter specifies whether our
 *  transmission should start in an odd or even-numbered timeslot.  To
 *  begin modulation in an odd-numbered timeslot, we must setup in
 *  an even-numbered timeslot.
 *
 *  We do nothing if the next timeslot is not appropriate.
 *
 **/
void Sequencer::actionPendXmit(unsigned oddEven, SequencerStateType newState) {
    oddEven &= 0x01;  // Force binary value:  1==odd, 0==even-numbered timeslot

    DFPRINTF("oddEven=%u, sequenceNumber=%lu newState=%u\n", oddEven, sequenceNumber, newState);

    // Arm the transmitter in the current timeslot if the required oddEven matches
    // the current sequenceNumber's oddEven to avoid doubling with the remote station.
    // This is where we decide if we can transmit in the next timeslot or if we
    // have to wait a while for the remote station to be listening.
    if (oddEven == ODD(sequenceNumber)) {
        Transmit_Armned = 1;                                // Yes, transmit in the next slot
        setup_to_transmit_on_next_DSP_Flag();               // loop() begins modulation in next timeslot
        state = newState;                                   // Advance state machine to new state after arming the transmitter
        ui.setXmitRecvIndicator(INDICATOR_ICON_TRANSMIT);   // Transmission will begin in loop()
        String thisTransmittedMsg = String(get_message());  // The pending outbound message text
        if (thisTransmittedMsg == lastTransmittedMsg) {
            lastStationMsgsItem = ui.theQSOMsgs->addStationMessageItem(ui.theQSOMsgs, thisTransmittedMsg, QSO_MSG_XMITRPT);  // Repeat transmission
        } else {
            lastStationMsgsItem = ui.theQSOMsgs->addStationMessageItem(ui.theQSOMsgs, thisTransmittedMsg, QSO_MSG_XMITING);  // New transmission
        }
        lastTransmittedMsg = thisTransmittedMsg;  // Remember for next time we add an item
        // DPRINTF("thisTransmittedMsg='%s'\n", thisTransmittedMsg.c_str());
    } else {
        ui.setXmitRecvIndicator(INDICATOR_ICON_PENDING);  // Transmission pending appropriate time slot
    }

}  // actionPendXmit()

/**
 *  @brief Helper routine to retrieve pointer to a decoded message
 *
 *  @param msgIndex Index of decoded message
 *
 *  @return pointer to Decode entry or NULL if msgIndex invalid
 *
 **/
extern Decode new_decoded[];  // References decode_ft8.cpp defining 20 elements
Decode* Sequencer::getDecodedMsg(unsigned msgIndex) {
    if (msgIndex < 20)
        return &new_decoded[msgIndex];
    else
        return NULL;
}

/**
 * @brief Getter for debugging sequenceNumber problems
 *
 * @return sequenceNumber
 *
 */
unsigned long Sequencer::getSequenceNumber() {
    return sequenceNumber;
}  // getSequenceNumber()

/**
 * @brief Get state for debugging Sequencer problems
 * @return state
 */
SequencerStateType Sequencer::getState() {
    return state;
}  // getState()

/**
 * @brief Start the QSO timeout timer
 *
 * The Timer was created and its interval established by begin().  Starting
 * a Timer effectively sets an alarm to expire at some later time.
 *
 * If/when a Timer expires, it notifies our onTimerEvent() callback function.
 * They typically expire when something expected fails to occur after some
 * reasonable time.
 *
 */
void Sequencer::startTimer() {
    timeoutTimer->start();
}

/**
 * @brief Stop the running timeout timer
 *
 * @note Timers are normally cancelled (stopped) as a QSO progresses normally.
 */
void Sequencer::stopTimer() {
    timeoutTimer->stop();
}

/**
 * @brief Helper routine to start a QSO
 * @param workedCall The remote station's callsign
 * @param oddEven Remote station expected to transmit in 1==odd, 0==even-numbered timeslots
 *
 * Manages details around starting a new QSO:
 *  + Initialize the contact object with information about this QSO
 *  + TODO:  Configure the UI for an active QSO
 *
 * @note Starting a QSO doesn't imply the contact will be successful as it may fail
 * for any of many reasons (QRM, QSB, QLF, QRT...).
 *
 */
void Sequencer::startQSO(const char* workedCall, unsigned oddEven) {
    static const char* emptyString = "";
    DTRACE();

    // Clear the CQ button
    ui.b0->reset();

    // Sanity check
    if (workedCall == NULL) workedCall = emptyString;

    // Activate this contact
    contact.begin(thisStation.getCallsign(), workedCall, thisStation.getFrequency(), "FT8", thisStation.getRig(), oddEven, thisStation.getSOTAref());

    // Record some info known about this contact
    contact.setRig(thisStation.getRig());            // Our rig description
    contact.setPwr(0.250);                           // Our power in watts, about 1/2 of a gerbil wheel                                                                                                 // Watts
    contact.setMyLocator(thisStation.getLocator());  // Our Maidenhead grid square
    contact.setMyName(thisStation.getMyName());      // Our operator's name

    // Setup UI to display an active QSO
    ui.setXmitRecvIndicator(INDICATOR_ICON_PENDING);  // Indicate we have a transmission pending

}  // startQSO

/**
 * @brief Terminate a QSO
 *
 * @note Helper routine manages a myriad of details around ending a QSO:
 *
 *  + Log a contact if sufficient info was obtained
 *  + Clear an outstanding FT8 message, if any
 *  + Clear the info display message, if any
 *  + Reset highlighted buttons
 *  + Cancel the timeout Timer
 *  + Switch from transmit to receive
 *
 * Note:  Upon entry, we expect the log contact structure to have the available
 * info about the ending QSO.  That info may or may not be complete (and thus the
 * QSO may or may not have been completed successfully).
 *
 * @note The contact object should have been a singleton as there is only one
 * and it's always instantiated.  Its begin() method initializes the contact
 * object state for a new QSO (marking it "active") and its reset() method
 * resets its state, making it "inactive."
 *
 * @note The Sequencer is allowed to invoke endQSO() to clean-up a potential QSO
 * whose contact object never even became active.  Likewise, a QSO might become
 * active without acquiring sufficient info about the remote station to be
 * considered a valid contact (for logging purposes).
 *
 * @note endQSO() should be invoked before assigning the next state because
 * endQSO() uses the current sequencer state to determine whether to log a
 * QSO or not.
 *
 */
void Sequencer::endQSO() {
    DTRACE();

    // Add some local parameters to the log's contact structure
    contact.setRig(thisStation.getRig());            // Pocket FT8 rig description
    contact.setPwr(0.250);                           // Watts
    contact.setMyLocator(thisStation.getLocator());  // Maidenhead grid square
    contact.setMyName(thisStation.getMyName());      // Operator's name if available

    // Only log the contact if we collected sufficient info about the remote station.
    // We are overly strict here (see the isValid() code) when compared to LoTW, but
    // comparable to SOTA/POTA any many other conventions.
    if (inQSO() && contact.isValid()) {
        DTRACE();
        contactLog->logContact(&contact);
        String str = String("Logged ") + String(contact.getWorkedCall());
        ui.applicationMsgs->setText(str);
    }

    // Cancel the QSO timeout Timer (if it's running)
    stopTimer();

    // Disarm the transmitter, clear the outbound message, and turn the receiver on
    xmit_flag = 0;                  // Stop modulation
    terminate_transmit_armed();     // Dis-arm the transmitter
    clearOutboundMessageDisplay();  // Clear displayed outbound message, if any
    clearOutboundMessageText();     // And clear the outbound message text string
    receive_sequence();             // Only need to do this if in-progress transmission aborted

    // Reset toggling GUI buttons
    // ui.b0->reset();  // Reset highlighted CQ button
    // ui.b2->reset();  // Reset highlighted TU button
    // Hmmm... are there others?  Should we just reset them all?  ToDo:  Look into this.
    ui.endQSO();  // Notify UI that this QSO, if any, is finished

    // Reset RoboOp's auto reply to received CQ messages.  If we left this active, RoboOp
    // would continue to make QSOs while we enjoy refreshments in the shade.
    // setAutoReplyToCQ(false);

    // We are finished with this contact object's info
    contact.reset();
    // ui.setXmitRecvIndicator(INDICATOR_ICON_RECEIVE);  // We are receiving again

}  // endQSO()

/**
 * @brief Determine if our station is in a QSO with any remote station
 * @return true if in QSO, false if not
 */
bool Sequencer::inQSO() {
    DTRACE();
    switch (state) {
        // Sequencer states when we are not in an active QSO
        case TUNING:       // TUNEing:  Transmitting unmodulated carrier
        case MSG_PENDING:  // 13-char (max) free text msg awaits a timeslot
        case XMIT_MSG:     // Transmit free text msg now
        case IDLE:         // IDLEing:  Not CQing, CALLing, QSOing nor TUNEing (just monitoring the traffic)
        case CQ_PENDING:   // CQing:  Awaiting timeslot after CQ button click
        case XMIT_CQ:      // CQing:  Transmitting our CQ
        case LISTEN_LOC:   // CQing:  Listening for any response with locator
        case LOC_PENDING:  // CALLing: Awaiting timeslot after known station's message click
        case XMIT_LOC:     // CALLing: Transmitting our locator in response to their CQ
        default:           // "A bottle of wine and a fifth of gin, and I'm lost in the ozone again" -- Commander Cody
            DPRINTF("Inactive QSO\n");
            return false;  // Not in an active QSO
            break;

        // Sequencer states during an active QSO
        case RSL_PENDING:   // QSOing: We are awaiting an appropriate timeslot to transmit an RSL
        case XMIT_RSL:      // QSOing: Transmitting their RSL
        case LISTEN_RRSL:   // QSOing: Listening for Roger and our RSL
        case RRR_PENDING:   // QSOing: We are awaiting an appropriate timeslot to transmit our RR73
        case XMIT_RRR:      // QSOing: Transmitting RR73
        case LISTEN_73:     // QSOing: Listening for their 73
        case LISTEN_RSL:    // QSOing: Listening for our RSL
        case RRSL_PENDING:  // QSOing: Awaiting timeslot to transmit RRSL (e.g. R-12)
        case XMIT_RRSL:     // QSOing: Transmitting Roger and their RSL
        case LISTEN_RRR:    // QSOing: Listen for their RRR/RR73/73
        case M73_PENDING:   // QSOing: Awaiting timeslot to transmit 73
        case XMIT_73:       // QSOing: Transmitting 73
            DPRINTF("Active QSO");
            return true;
            break;
    }
}  // inQSO()

/**
 * @brief Determine if our station is in QSO with the specified remote station
 * @param callSign Remote station's callsign
 * @return true if in QSO, false otherwise
 */
bool Sequencer::inQSO(String callSign) {
    DTRACE();
    if (inQSO() && callSign.equals(thisStation.getCallsign())) {
        DPRINTF("In QSO with %s\n", thisStation.getCallsign());
        return true;
    }
    DPRINTF("Not in QSO with %s\n", thisStation.getCallsign());
    return false;
}

/**
 * @brief Setter for autoReplyToCQ
 * @param x true enables auto reply to CQ
 *
 * The RoboOp sequencer automatically replies to a non-directed CQ message if
 * autoReplyToCQ==true.
 *
 * Our Operator uses the TX button to enable auto-replies.  We reset the Tx
 * button when autoReply clears.
 *
 */
void setAutoReplyToCQ(bool x) {
    autoReplyToCQ = x;
    DPRINTF("autoReplyToCQ=%d\n", autoReplyToCQ);
    if (!autoReplyToCQ) {
        ui.b3->reset();  // Reset highlighted button
    }
}

/**
 * @brief getter for autoReplyToCQ
 * @return true or false
 */
bool getAutoReplyToCQ() {
    return autoReplyToCQ;
}

/**
 * @brief Highlight the lastTransmittedMsg if it timed-out
 *
 * @note Rather than consume additional UI space informing the operator of
 * the time-out, we simply highlight (recolor) our message that never
 * received a satisfactory response from the remote station.
 */
void Sequencer::highlightAbortedTransmission() {
    DTRACE();
    String thisTransmittedMsg = String(get_message());  // The pending outbound message text
    if (thisTransmittedMsg == lastTransmittedMsg) {
        ui.theQSOMsgs->setItemColors(lastStationMsgsItem, A_RED, A_BLACK);  // Recolor previous (retransmitted) msg
    }
}  // highlightAbortedTransmission()

/**
 * @brief Setup the transmitter to respond to a CQ at their offset frequency
 * @param cursorFreq The Waterfall cursor offset in Hz from the carrier frequency
 */
void set_Target_Frequency(int cursorFreq) {
    thisStation.setCursorFreq(/*(float)*/ cursorFreq);
    set_Xmit_Freq();
    // String str = String("Cursor freq = ") + String(thisStation.getCursorFreq()) + String(" Hz");
    //  DPRINTF("%s\n", str.c_str());
    //  ui.applicationMsgs->setText(str);
    ui.setCursorLine(cursorFreq);
    ui.displayFrequency();  // Update station info display too

    // TODO:  Move cursor_line pixel calculations into UI
    // cursor_line = (uint16_t)((float)cursorFreq / FFT_Resolution);
    // cursor_line = cursor_line - ft8_min_bin;
}
