conr2286/PocketFT8Xcvr/PocketFT8XcvrFW/src/gen_ft8.cpp

/*
 * gen_ft8.c
 *
 *  Created on: Oct 24, 2019
 *      Author: user
 */

#include "gen_ft8.h"

#include <TimeLib.h>
#include <math.h>
#include <stdio.h>
#include <stdlib.h>
#include <string.h>

#include "HX8357_t3n.h"
#include "NODEBUG.h"
#include "constants.h"
#include "encode.h"
#include "pack.h"
extern HX8357_t3n tft;

#include <string.h>

#include "arm_math.h"
#include "decode_ft8.h"
// #include "display.h"
#include "locator.h"
#include "UserInterface.h"
#include "msgTypes.h"
#include "traffic_manager.h"
#include "PocketFT8Xcvr.h"
#include "message.h"

// char Your_Call[] = "W5XXX";
// char Your_Locator[] = "AA00";

// char test_station[] = "W5BAA";
// char test_target[] = "W5ITU";
// char test_RSL[] = "R-15";

char Target_Call[FTX_NONSTANDARD_CALLSIGN_BFRSIZE];     // 11 character call sign + /0
char Target_Locator[FTX_REPORTS_BFRSIZE];               // four character locator  + /0
int Target_RSL;                                         // their RSL
char CQ_Target_Call[FTX_NONSTANDARD_CALLSIGN_BFRSIZE];  // 11 character call sign + /0

char reply_message[FTX_MAX_MESSAGE_LENGTH];
char reply_message_list[FTX_MAX_MESSAGE_LENGTH][8];
int reply_message_count;
char message[FTX_MAX_MESSAGE_LENGTH];  // FT8 message text pending transmission (w/hashed callsigns)
int message_state;                     // Non-zero => message[] is valid/ready (but nothing checks it???)

// extern int log_flag, logging_on;
extern time_t getTeensy3Time();

// char ft8_time_string[] = "15:44:15";

static UserInterface& ui = UserInterface::getInstance();
static Station& thisStation = Station::getInstance();

const int max_displayed_messages = 8;

static bool isStandardCallsign(const char* s);

/**
 * Setup required parameters for constructing messages to remote target station
 *
 * @param targetCall The remote station's callsign
 * @param rsl The remote station's RSL report
 *
 *
 **/
void setXmitParams(char* targetCall, int rsl) {
    strlcpy(Target_Call, targetCall, sizeof(Target_Call));
    Target_RSL = rsl;
}

/**
 * Retrieves the outbound message char[] string
 *
 * @return pointer to the outbound message char[] string
 *
 **/
char* get_message() {
    return message;
}

/**
 *  Builds an outbound FT8 standard message[] for later transmission
 *
 *  Constructs and displays the specified FT8 outbound message and sets the
 *  message_state flag indicating message[] is valid.  Does not actually
 *  start the transmitter.
 *
 *  Global variable usage includes:
 *    Station_Call[] -- Our station's callsign
 *    Locator[] --      Our station's maidenhead gridsquare
 *    TargetCall --     Worked station's callsign
 *    TargetRSL --      Worked station's Received Signal Level
 *    message[] --      The outbound message is constructed here
 *    message_state --  Status of message[]: 0==Invalid, 1==Valid
 *    tones[] --        Outbound message tones for the modulator
 *
 *  @param index Specifies the outbound FT8 message type, e.g.
 *              0 -- CQ KQ7B DN15
 *              1 -- W1AW KQ7B DN15
 *              2 -- W1AW KQ7B -12
 *              3 -- W1AW KQ7B RR73
 *              4 -- W1AW KQ7B R-8
 *              5 -- W1AW KQ7B RRR
 *
 **/
void set_message(uint16_t index) {
    uint8_t packed[K_BYTES];
    char seventy_three[] = "RR73";

    DPRINTF("set_message(%u)\n", index);

    clearOutboundMessageText();
    clearOutboundMessageDisplay();

    const char* locator = thisStation.getLocator();
    const char* ourCall = thisStation.getCallsign();
    const char* nil = "";

    // Build the message text specified by index
    switch (index) {
        case MSG_CQ:                                          // We are calling CQ from our Locator, e.g. CQ KQ7B DN15
            if (!isStandardCallsign(ourCall)) locator = nil;  // Nonstandard calls xmit as nonstandard message
            snprintf(message, sizeof(message), "%s %s %s", "CQ", ourCall, locator);
            break;

        case MSG_LOC:                                                                             // We are calling target station from our Locator, e.g. W1AW KQ7B DN15
            if (!isStandardCallsign(ourCall) || !isStandardCallsign(Target_Call)) locator = nil;  // Nonstandard calls xmit as nonstandard message
            snprintf(message, sizeof(message), "%s %s %s", Target_Call, ourCall, locator);
            break;

        case MSG_RSL:  // We are responding to target with their signal report, e.g. W1AW KQ7B -12
            snprintf(message, sizeof(message), "%s %s %i", Target_Call, thisStation.getCallsign(), Target_RSL);
            break;

        case MSG_RR73:  // We are responding to target with RR73, e.g. W1AW KQ7B RR73
            snprintf(message, sizeof(message), "%s %s %3s", Target_Call, thisStation.getCallsign(), seventy_three);
            break;

        case MSG_73:  // We are responding to target with 73, e.g. W1AW KQ7B 73
            snprintf(message, sizeof(message), "%s %s %s", Target_Call, thisStation.getCallsign(), "73");
            break;

        case MSG_RRSL:  // We are responding with Roger and their RRSL signal report, e.g. W1AW KQ7B R-3
            snprintf(message, sizeof(message), "%s %s R%i", Target_Call, thisStation.getCallsign(), Target_RSL);
            break;

        case MSG_RRR:  // We are responding with RRR, e.g. W1AW KQ7B RRR
            snprintf(message, sizeof(message), "%s %s RRR", Target_Call, thisStation.getCallsign());
            break;

        default:
            DPRINTF("***** ERROR:  Invalid set_message(%d) index\n", index);
            break;
    }

    // Display the outbound message text
    DPRINTF("generated text message='%s'\n", message);
    ui.theQSOMsgs->addStationMessageItem(ui.theQSOMsgs, String(message), QSO_MSG_XMITPEND);

    //  TODO:  Nonstandard callsigns
    //  Messages sent from our nonstandard callsign:
    //      CQ KQ7B/IDAHO           -- MSG_CQ  packs as type 4, nonstandard message
    //      W1AW KQ7B/IDAHO DN15    -- MSG_LOC packs as type 4, nonstandard message sans the locator
    //  Messages sent to a nonstandard callsign:
    //  CN/W1AW KQ7B DN15       -- MSG_LOC packs as type 1, standard message with hashed dest callsign
    // pack77_1(message, packed);
    pack77(message, packed);
    genft8(packed, tones);

    message_state = 1;

    // DPRINTF("message='%s'\n", message);

}  // set_message()

/**
 * @brief Set up a 13-char (max) free text for transmission
 * @param freeText The message
 */
void set_message(char* freeText) {
    uint8_t packed[K_BYTES];

    DPRINTF("set_message(%s)\n", freeText);

    // Ignore nonsense
    if ((freeText == NULL) || (strlen(freeText) == 0)) return;

    // strlcpy(message, blank, sizeof(message));
    clearOutboundMessageText();
    clearOutboundMessageDisplay();

    snprintf(message, sizeof(message), "%s", freeText);
    DPRINTF("message='%s'\n", message);
    // ui.applicationMsgs->setText(message);
    ui.theQSOMsgs->addStationMessageItem(ui.theQSOMsgs, String("foo"), QSO_MSG_DEBUG);

    // Prepare the outbound message as an array of tones for the FSK modulator
    // packtext77(message, packed);  // Pack text into compressed bit
    pack77(message, packed);  // Pack text into compressed bits
    genft8(packed, tones);    // Generate the FT8 tones for modulator

    message_state = 1;

    // DPRINTF("message='%s'\n", message);
}

void clearOutboundMessageText(void) {
    // char blank[] = "                   ";
    // strlcpy(message, blank, sizeof(message));
    message[0] = 0;
}

void clearOutboundMessageDisplay(void) {
    // DTRACE();

    // char blank[] = "                      ";
    // tft.setTextColor(HX8357_YELLOW, HX8357_BLACK);
    // // tft.setTextSize(2);
    // tft.setCursor(DISPLAY_OUTBOUND_X, DISPLAY_OUTBOUND_Y);
    // tft.print(blank);
    message_state = 0;
}

//?????
void clear_reply_message_box(void) {
    tft.fillRect(0, 100, 400, 140, HX8357_BLACK);
}

/**
 * @brief Determine if a callsign is an FT8 standard callsign
 * @param callsign text string
 * @return true==standard
 */
bool isStandardCallsign(const char* callsign) {
    if (pack_basecall(callsign, strlen(callsign)) < 0) return false;
    return true;  // Will report CQ as a callsign
}
