conr2286/PocketFT8Xcvr/PocketFT8XcvrFW/include/PocketFT8Xcvr.h

#pragma once

#include <Arduino.h>

#include "Config.h"
#include "Station.h"
#include "UserInterface.h"

// Global objects widely accessed
// extern Station thisStation;
extern ConfigType config;
// extern UserInterface& ui;
