conr2286/PocketFT8Xcvr/PocketFT8XcvrFW/include/msgTypes.h

#pragma once

/**
 * @brief Define the legacy FT8_LIB decoded messge types
 *
 * @note While modern versions of ft8_lib no longer return these, they are
 * scattered throughout the Pocket FT8 implementation.
 *
 * @note Modern versions of ft8_lib no longer identify MSG_BLANK.  The
 * decoder abstracts away the unique features of the ft8 nonstandard message.
 */
typedef enum MsgTypeValues {
    MSG_CQ = 0,       // CQ/QRZ and Locator (e.g. CQ KQ7B DN15) messagen
    MSG_LOC = 1,      // Locator (e.g. AG03 KQ7B DN15, or W1AW KQ7B R DN15) message
    MSG_RSL = 2,      // Received signal level (e.g. W1AW KQ7B -10) message
    MSG_RRSL = 3,     // Roger report and here's your RSL (e.g. W1AW KQ7B R-10)
    MSG_RR73 = 4,     // Roger report and 73
    MSG_RRR = 5,      // Roger and your RSL (e.g. W1AW KQ7B R-10) message
    MSG_73 = 6,       // Received end-of-transmission (e.g. RRR, RR73 or 73) message
    MSG_BLANK = 7,    // Received non-standard (hashed callsign) with a blank field3
    MSG_FREE = 8,     // Free text in field1 (e.g. TNX BOB 73 GL)
    MSG_TELE = 9,     // Telemetry (hexadecimal digits) in field1
    MSG_UNKNOWN = 10  // Something we couldn't decode
} MsgType;
