conr2286/PocketFT8Xcvr/PocketFT8XcvrFW/include/unity_config.h

#ifndef UNITY_CONFIG_H
#define UNITY_CONFIG_H

/* Generated unity configuration for PlatformIO */
/* This file is for IntelliSense support only */

#define UNITY_INCLUDE_DOUBLE
#define UNITY_INT_WIDTH 32
#define UNITY_POINTER_WIDTH 32
#define UNITY_SUPPORT_64

#endif /* UNITY_CONFIG_H */
