conr2286/PocketFT8Xcvr/PocketFT8XcvrFW/src/gen_ft8.h

/*
 * gen_ft8.h
 *
 *  Created on: Oct 30, 2019
 *      Author: user
 */

#ifndef GEN_FT8_H_
#define GEN_FT8_H_

#include "arm_math.h"
// char Locator[5]; // four character locator  + /0
// char Station_Call[7]; //six character call sign + /0

void clear_reply_message_box(void);

void set_reply(uint16_t index);
void set_cq(void);
void set_CQ_reply(void);

void Open_Station_File(void);
void Write_Station_File(void);
void Read_Station_File(void);
void Station_Data_Initialize(void);

char* get_message();
void set_message(uint16_t index);
void set_message(char* freeText);
void clearOutboundMessageDisplay(void);
void setXmitParams(char* targetStation, int snr);
void clearOutboundMessageText(void);

#endif /* GEN_FT8_H_ */
