conr2286/PocketFT8Xcvr/PocketFT8XcvrFW/src/WF_Table.h

/*
 * WF_Table.h
 *
 *  Created on: Dec 25, 2018
 *      Author: user
 */

#ifndef WF_TABLE_H_
#define WF_TABLE_H_
const PROGMEM uint16_t WFPalette[64] = {
0x0000, 
0x0000, 
0x0000, 
0x0000, 
0x0000, 
0x0000, 
0x0000, 
0x0000, 
0x28B9,
0x28B9,
0x28B9,
0x28B9,
0x28B9,
0x28B9,
0x28B9,
0x28B9,
0xC8B5,
0xC8B5,
0xC8B5,
0xC8B5,
0xC8B5,
0xC8B5,
0xC8B5,
0xC8B5,
0x1619, 
0x1619, 
0x1619, 
0x1619, 
0x1619, 
0x1619, 
0x1619, 
0x1619, 
0x1CE5, 
0x1CE5, 
0x1CE5, 
0x1CE5, 
0x1CE5, 
0x1CE5, 
0x1CE5, 
0x1CE5, 
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

};

#endif /* WF_TABLE_H_ */
