conr2286/PocketFT8Xcvr/PocketFT8XcvrFW/Project Driver Files/HX8357_t3-master/HX8357_font_Arial.h

#ifndef _HX8357_t3_font_Arial_
#define _HX8357_t3_font_Arial_

#include "HX8357_t3.h"

#ifdef __cplusplus
extern "C" {
#endif

extern const HX8357_t3_font_t Arial_8;
extern const HX8357_t3_font_t Arial_9;
extern const HX8357_t3_font_t Arial_10;
extern const HX8357_t3_font_t Arial_11;
extern const HX8357_t3_font_t Arial_12;
extern const HX8357_t3_font_t Arial_13;
extern const HX8357_t3_font_t Arial_14;
extern const HX8357_t3_font_t Arial_16;
extern const HX8357_t3_font_t Arial_18;
extern const HX8357_t3_font_t Arial_20;
extern const HX8357_t3_font_t Arial_24;
extern const HX8357_t3_font_t Arial_28;
extern const HX8357_t3_font_t Arial_32;
extern const HX8357_t3_font_t Arial_40;
extern const HX8357_t3_font_t Arial_48;
extern const HX8357_t3_font_t Arial_60;
extern const HX8357_t3_font_t Arial_72;
extern const HX8357_t3_font_t Arial_96;

#ifdef __cplusplus
} // extern "C"
#endif

#endif
