conr2286/PocketFT8Xcvr/PocketFT8XcvrFW/Project Driver Files/HX8357_t3-master/HX8357_font_ArialBold.h

#ifndef _HX8357_t3_font_ArialBold_
#define _HX8357_t3_font_ArialBold_

#include "HX8357_t3.h"

#ifdef __cplusplus
extern "C" {
#endif

extern const HX8357_t3_font_t Arial_8_Bold;
extern const HX8357_t3_font_t Arial_9_Bold;
extern const HX8357_t3_font_t Arial_10_Bold;
extern const HX8357_t3_font_t Arial_11_Bold;
extern const HX8357_t3_font_t Arial_12_Bold;
extern const HX8357_t3_font_t Arial_13_Bold;
extern const HX8357_t3_font_t Arial_14_Bold;
extern const HX8357_t3_font_t Arial_16_Bold;
extern const HX8357_t3_font_t Arial_18_Bold;
extern const HX8357_t3_font_t Arial_20_Bold;
extern const HX8357_t3_font_t Arial_24_Bold;
extern const HX8357_t3_font_t Arial_28_Bold;
extern const HX8357_t3_font_t Arial_32_Bold;
extern const HX8357_t3_font_t Arial_40_Bold;
extern const HX8357_t3_font_t Arial_48_Bold;
extern const HX8357_t3_font_t Arial_60_Bold;
extern const HX8357_t3_font_t Arial_72_Bold;
extern const HX8357_t3_font_t Arial_96_Bold;

#ifdef __cplusplus
} // extern "C"
#endif

#endif
