conr2286/PocketFT8Xcvr/BenchTests/Test01-Blinky/Test01-Blinky.ino

/*
NAME
  Blink -- Turns Teensy 4.1 on-board LED on for one second, then off for one second, repeatedly.

DESCRIPTION

EXERCISED
  This most basic of tests exercises the Arduino development environment's support for Teensy and
  verifies the MPU powers up, loads and executes programs sans smoke

ATTRIBUTION
  modified 8 May 2014
  by Scott Fitzgerald
  modified 2 Sep 2016
  by Arturo Guadalupi
  modified 8 Sep 2016
  by Colby Newman

  This example code is in the public domain.

  https://www.arduino.cc/en/Tutorial/BuiltInExamples/Blink
*/

// the setup function runs once when you press reset or power the board
void setup() {
  // initialize digital pin LED_BUILTIN as an output.
  pinMode(LED_BUILTIN, OUTPUT);
}

// the loop function runs over and over again forever
void loop() {
  digitalWrite(LED_BUILTIN, HIGH);  // turn the LED on (HIGH is the voltage level)
  delay(1000);                      // wait for a second
  digitalWrite(LED_BUILTIN, LOW);   // turn the LED off by making the voltage LOW
  delay(5000);                      // wait for a second
}
