conr2286/PocketFT8Xcvr/BenchTests/Test05-TouchScreen/HX8357_t3n.cpp

// https://github.com/PaulStoffregen/ILI9341_t3n
// http://forum.pjrc.com/threads/26305-Highly-optimized-ILI9341-(320x240-TFT-color-display)-library

/***************************************************
  This is our library for the Adafruit ILI9341 Breakout and Shield
  ----> http://www.adafruit.com/products/1651

  Check out the links above for our tutorials and wiring diagrams
  These displays use SPI to communicate, 4 or 5 pins are required to
  interface (RST is optional)
  Adafruit invests time and resources providing this open source code,
  please support Adafruit and open-source hardware by purchasing
  products from Adafruit!

  Written by Limor Fried/Ladyada for Adafruit Industries.
  MIT license, all text above must be included in any redistribution
 ****************************************************/
// <SoftEgg>

//Additional graphics routines by Tim Trzepacz, SoftEgg LLC added December 2015
//(And then accidentally deleted and rewritten March 2016. Oops!)
//Gradient support
//----------------
//		fillRectVGradient	- fills area with vertical gradient
//		fillRectHGradient	- fills area with horizontal gradient
//		fillScreenVGradient - fills screen with vertical gradient
// 	fillScreenHGradient - fills screen with horizontal gradient

//Additional Color Support
//------------------------
//		color565toRGB		- converts 565 format 16 bit color to RGB
//		color565toRGB14		- converts 16 bit 565 format color to 14 bit RGB (2 bits clear for math and sign)
//		RGB14tocolor565		- converts 14 bit RGB back to 16 bit 565 format color

//Low Memory Bitmap Support
//-------------------------
// 		writeRect8BPP - 	write 8 bit per pixel paletted bitmap
// 		writeRect4BPP - 	write 4 bit per pixel paletted bitmap
// 		writeRect2BPP - 	write 2 bit per pixel paletted bitmap
// 		writeRect1BPP - 	write 1 bit per pixel paletted bitmap

//TODO: transparent bitmap writing routines for sprites

//String Pixel Length support
//---------------------------
//		strPixelLen			- gets pixel length of given ASCII string

// <\SoftEgg>

#include "HX8357_t3n.h"
#include <SPI.h>  

//#define DEBUG_ASYNC_UPDATE  // Enable to print out dma info
//#define DEBUG_ASYNC_LEDS	// Enable to use digitalWrites to Debug
#ifdef DEBUG_ASYNC_LEDS
#define DEBUG_PIN_1 4
#define DEBUG_PIN_2 5
#define DEBUG_PIN_3 6
#endif

#ifdef ENABLE_HX8357_FRAMEBUFFER
#define CBALLOC (HX8357_TFTHEIGHT*HX8357_TFTWIDTH*2)
#define	COUNT_WORDS_WRITE  ((HX8357_TFTHEIGHT*HX8357_TFTWIDTH)/SCREEN_DMA_NUM_SETTINGS) // Note I know the divide will give whole number

#if defined(__MK66FX1M0__) 
	// T3.6 use Scatter/gather with chain to do transfer
DMASetting 	HX8357_t3n::_dmasettings[4];
DMAChannel 	HX8357_t3n::_dmatx;
#elif defined(__IMXRT1052__) || defined(__IMXRT1062__)  // Teensy 4.x
// Settings are part of the actual object not static... 
//DMASetting 	HX8357_t3n::_dmasettings[4];
//DMAChannel 	HX8357_t3n::_dmatx;
#else
// T3.5 - had issues scatter/gather so do just use channels/interrupts
// and update and continue
DMAChannel  HX8357_t3n::_dmatx;
DMAChannel  HX8357_t3n::_dmarx;
uint16_t 	HX8357_t3n::_dma_count_remaining;
uint16_t	HX8357_t3n::_dma_write_size_words;
volatile short _dma_dummy_rx;
#endif	

#if defined(__IMXRT1052__) || defined(__IMXRT1062__)  // Teensy 4.x
HX8357_t3n *HX8357_t3n::_dmaActiveDisplay[3] = {0, 0, 0};
#else
HX8357_t3n *HX8357_t3n::_dmaActiveDisplay = 0;
#endif

//volatile uint8_t  	HX8357_t3n::_dma_state = 0;  // Use pointer to this as a way to get back to object...
//volatile uint32_t	HX8357_t3n::_dma_frame_count = 0;	// Can return a frame count...


#if defined(__IMXRT1052__) || defined(__IMXRT1062__)  // Teensy 4.x
void HX8357_t3n::dmaInterrupt(void) {
	if (_dmaActiveDisplay[0])  {
		_dmaActiveDisplay[0]->process_dma_interrupt();
	}
}
void HX8357_t3n::dmaInterrupt1(void) {
	if (_dmaActiveDisplay[1])  {
		_dmaActiveDisplay[1]->process_dma_interrupt();
	}
}
void HX8357_t3n::dmaInterrupt2(void) {
	if (_dmaActiveDisplay[2])  {
		_dmaActiveDisplay[2]->process_dma_interrupt();
	}
}


#else
void HX8357_t3n::dmaInterrupt(void) {
	if (_dmaActiveDisplay)  {
		_dmaActiveDisplay->process_dma_interrupt();
	}
}
#endif

#ifdef DEBUG_ASYNC_UPDATE
extern void dumpDMA_TCD(DMABaseClass *dmabc);
#endif

void HX8357_t3n::process_dma_interrupt(void) {
#ifdef DEBUG_ASYNC_LEDS
	digitalWriteFast(DEBUG_PIN_2, HIGH);
#endif
#if defined(__MK66FX1M0__) 
	// T3.6
	_dma_frame_count++;
	_dmatx.clearInterrupt();

	// See if we are in continuous mode or not..
	if ((_dma_state & HX8357_DMA_CONT) == 0) {
		// We are in single refresh mode or the user has called cancel so
		// Lets try to release the CS pin
		waitFifoNotFull();
		writecommand_last(HX8357_NOP);
		endSPITransaction();
		_dma_state &= ~HX8357_DMA_ACTIVE;
		_dmaActiveDisplay = 0;	// We don't have a display active any more... 

	}
#elif defined(__IMXRT1052__) || defined(__IMXRT1062__)  // Teensy 4.x
	// T4
	#if defined(TRY_FULL_DMA_CHAIN)
	_dma_frame_count++;
	_dmatx.clearInterrupt();
	//Serial.print(".");
	#ifdef DEBUG_ASYNC_LEDS
		digitalWriteFast(DEBUG_PIN_3, HIGH);
	#endif
	// See if we are in continuous mode or not..
	if ((_dma_state & HX8357_DMA_CONT) == 0) {
		// We are in single refresh mode or the user has called cancel so
		// Lets try to release the CS pin
		//Serial.printf("Before FSR wait: %x %x\n", _pimxrt_spi->FSR, _pimxrt_spi->SR);
		while (_pimxrt_spi->FSR & 0x1f)  ;	// wait until this one is complete

		//Serial.printf("Before SR busy wait: %x\n", _pimxrt_spi->SR);
		while (_pimxrt_spi->SR & LPSPI_SR_MBF)  ;	// wait until this one is complete

		_dmatx.clearComplete();
		//Serial.println("Restore FCR");
		_pimxrt_spi->FCR = LPSPI_FCR_TXWATER(15); // _spi_fcr_save;	// restore the FSR status... 
 		_pimxrt_spi->DER = 0;		// DMA no longer doing TX (or RX)

		_pimxrt_spi->CR = LPSPI_CR_MEN | LPSPI_CR_RRF | LPSPI_CR_RTF;   // actually clear both...
		_pimxrt_spi->SR = 0x3f00;	// clear out all of the other status...

		maybeUpdateTCR(_tcr_dc_assert | LPSPI_TCR_FRAMESZ(7));	// output Command with 8 bits
		// Serial.printf("Output NOP (SR %x CR %x FSR %x FCR %x %x TCR:%x)\n", _pimxrt_spi->SR, _pimxrt_spi->CR, _pimxrt_spi->FSR, 
		//	_pimxrt_spi->FCR, _spi_fcr_save, _pimxrt_spi->TCR);
		writecommand_last(HX8357_NOP);
		endSPITransaction();
		_dma_state &= ~HX8357_DMA_ACTIVE;
		_dmaActiveDisplay[_spi_num]  = 0;	// We don't have a display active any more... 
	} else {
		// Lets try to flush out memory
		if ((uint32_t)_pfbtft >= 0x20200000u)  arm_dcache_flush(_pfbtft, CBALLOC);
	}
	#ifdef DEBUG_ASYNC_LEDS
		digitalWriteFast(DEBUG_PIN_3, LOW);
	#endif
	#else
	bool still_more_dma = true;
	_dma_sub_frame_count++;
	//	Serial.print(".");
	if (_dma_sub_frame_count == _dma_cnt_sub_frames_per_frame) {
	#ifdef DEBUG_ASYNC_LEDS
		digitalWriteFast(DEBUG_PIN_3, HIGH);
	#endif
		//Serial.println("*");
		// We completed a frame. 
		_dma_frame_count++;
		// See if we are logically done
		if (_dma_state & HX8357_DMA_FINISH) {
			//Serial.println("$");
			still_more_dma = false;

			// We are in single refresh mode or the user has called cancel so
			// Lets try to release the CS pin
			// Lets wait until FIFO is not empty
			//Serial.printf("Before FSR wait: %x %x\n", _pimxrt_spi->FSR, _pimxrt_spi->SR);
			while (_pimxrt_spi->FSR & 0x1f)  ;	// wait until this one is complete

			//Serial.printf("Before SR busy wait: %x\n", _pimxrt_spi->SR);
			while (_pimxrt_spi->SR & LPSPI_SR_MBF)  ;	// wait until this one is complete

			_dmatx.clearComplete();
			//Serial.println("Restore FCR");
			_pimxrt_spi->FCR = LPSPI_FCR_TXWATER(15); // _spi_fcr_save;	// restore the FSR status... 
	 		_pimxrt_spi->DER = 0;		// DMA no longer doing TX (or RX)

			_pimxrt_spi->CR = LPSPI_CR_MEN | LPSPI_CR_RRF | LPSPI_CR_RTF;   // actually clear both...
			_pimxrt_spi->SR = 0x3f00;	// clear out all of the other status...


			maybeUpdateTCR(_tcr_dc_assert | LPSPI_TCR_FRAMESZ(7));	// output Command with 8 bits
			// Serial.printf("Output NOP (SR %x CR %x FSR %x FCR %x %x TCR:%x)\n", _pimxrt_spi->SR, _pimxrt_spi->CR, _pimxrt_spi->FSR, 
			//	_pimxrt_spi->FCR, _spi_fcr_save, _pimxrt_spi->TCR);
			writecommand_last(HX8357_NOP);

			// Serial.println("Do End transaction");
			endSPITransaction();
			_dma_state &= ~(HX8357_DMA_ACTIVE | HX8357_DMA_FINISH);
			_dmaActiveDisplay[_spi_num]  = 0;	// We don't have a display active any more... 

 			// Serial.println("After End transaction");
			//Serial.println("$");
		}
		_dma_sub_frame_count = 0;
#ifdef DEBUG_ASYNC_LEDS
		digitalWriteFast(DEBUG_PIN_3, LOW);
#endif
	}

	if (still_more_dma) {
		// we are still in a sub-frame so we need to copy memory down...
		if (_dma_sub_frame_count == (_dma_cnt_sub_frames_per_frame-2)) {
			if ((_dma_state & HX8357_DMA_CONT) == 0) {
				if (_dma_sub_frame_count & 1) _dmasettings[0].disableOnCompletion();
				else _dmasettings[1].disableOnCompletion();
				//Serial.println("!");
				_dma_state |= HX8357_DMA_FINISH;  // let system know we set the finished state

			}
		}
		if (_dma_sub_frame_count & 1) {
			memcpy(_dma_buffer1, &_pfbtft_async[_dma_pixel_index], _dma_buffer_size*2);
		} else {			
			memcpy(_dma_buffer2, &_pfbtft_async[_dma_pixel_index], _dma_buffer_size*2);
		}
		_dma_pixel_index += _dma_buffer_size;
		if (_dma_pixel_index >= (_count_pixels))
			_dma_pixel_index = 0;		// we will wrap around 
	}
	_dmatx.clearInterrupt();
	_dmatx.clearComplete();
#endif
	asm("dsb");

#else
	// T3.5...
	_dmarx.clearInterrupt();
	_dmatx.clearComplete();
	_dmarx.clearComplete();

	if (!_dma_count_remaining && !(_dma_state & HX8357_DMA_CONT)) {
		// The DMA transfers are done.
		_dma_frame_count++;
#ifdef DEBUG_ASYNC_LEDS
		digitalWriteFast(DEBUG_PIN_3, HIGH);
#endif

		_pkinetisk_spi->RSER = 0;
		//_pkinetisk_spi->MCR = SPI_MCR_MSTR | SPI_MCR_CLR_RXF | SPI_MCR_PCSIS(0x1F);  // clear out the queue
		_pkinetisk_spi->SR = 0xFF0F0000;
		_pkinetisk_spi->CTAR0  &= ~(SPI_CTAR_FMSZ(8)); 	// Hack restore back to 8 bits

		writecommand_last(HX8357_NOP);
		endSPITransaction();
		_dma_state &= ~HX8357_DMA_ACTIVE;
		_dmaActiveDisplay = 0;	// We don't have a display active any more... 
#ifdef DEBUG_ASYNC_LEDS
		digitalWriteFast(DEBUG_PIN_3, LOW);
#endif

	} else {
		uint16_t w;
		if (_dma_count_remaining) { // Still part of one frome. 
			_dma_count_remaining -= _dma_write_size_words;
			w = *((uint16_t*)_dmatx.TCD->SADDR);
			_dmatx.TCD->SADDR = (volatile uint8_t*)(_dmatx.TCD->SADDR) + 2;
		} else {  // start a new frame
			_dma_frame_count++;
			_dmatx.sourceBuffer(&_pfbtft[1], (_dma_write_size_words-1)*2);
			_dmatx.TCD->SLAST = 0;	// Finish with it pointing to next location
			w = _pfbtft[0];
			_dma_count_remaining = CBALLOC/2 - _dma_write_size_words;	// how much more to transfer? 
		}
#ifdef DEBUG_ASYNC_UPDATE
//		dumpDMA_TCD(&_dmatx);
//		dumpDMA_TCD(&_dmarx);
#endif
		_pkinetisk_spi->PUSHR = (w | SPI_PUSHR_CTAS(0) | SPI_PUSHR_CONT);
		_dmarx.enable();
		_dmatx.enable();
	}

#endif	
#ifdef DEBUG_ASYNC_LEDS
	digitalWriteFast(DEBUG_PIN_2, LOW);
#endif
}

#endif
// Teensy 3.1 can only generate 30 MHz SPI when running at 120 MHz (overclock)

#define WIDTH  HX8357_TFTWIDTH
#define HEIGHT HX8357_TFTHEIGHT

// Constructor when using hardware ILI9241_KINETISK__pspi->  Faster, but must use SPI pins
// specific to each board type (e.g. 11,13 for Uno, 51,52 for Mega, etc.)
HX8357_t3n::HX8357_t3n(uint8_t cs, uint8_t dc, uint8_t rst, 
	uint8_t mosi, uint8_t sclk, uint8_t miso)
{
	_cs   = cs;
	_dc   = dc;
	_rst  = rst;
	_mosi = mosi;
	_sclk = sclk;
	_miso = miso;
	_width    = WIDTH;
	_height   = HEIGHT;

	rotation  = 0;
	cursor_y  = cursor_x    = 0;
	textsize_x = textsize_y  = 1;
	textcolor = textbgcolor = 0xFFFF;
	wrap      = true;
	font      = NULL;
	gfxFont   = NULL;
	setClipRect();
	setOrigin();

	// Added to see how much impact actually using non hardware CS pin might be
    _cspinmask = 0;
    _csport = NULL;

	#ifdef ENABLE_HX8357_FRAMEBUFFER
    _pfbtft = NULL;	
    _use_fbtft = 0;						// Are we in frame buffer mode?
	_we_allocated_buffer = NULL;
    #endif

}

//=======================================================================
// Add optinal support for using frame buffer to speed up complex outputs
//=======================================================================
void HX8357_t3n::setFrameBuffer(uint16_t *frame_buffer) 
{
	#ifdef ENABLE_HX8357_FRAMEBUFFER
	_pfbtft = frame_buffer;
	/*  // Maybe you don't want the memory cleared as you may be playing games wiht multiple buffers. 
	if (_pfbtft != NULL) {
		memset(_pfbtft, 0, HX8357_TFTHEIGHT*HX8357_TFTWIDTH*2);
	}
	*/
	_dma_state &= ~HX8357_DMA_INIT; // clear that we init the dma chain as our buffer has changed... 

	#endif	
}

uint8_t HX8357_t3n::useFrameBuffer(boolean b)		// use the frame buffer?  First call will allocate
{
	#ifdef ENABLE_HX8357_FRAMEBUFFER

	if (b) {
		// First see if we need to allocate buffer
		if (_pfbtft == NULL) {
			// Hack to start frame buffer on 32 byte boundary
			_we_allocated_buffer = (uint16_t *)malloc(CBALLOC+32);
			if (_we_allocated_buffer == NULL)
				return 0;	// failed 
			_pfbtft = (uint16_t*) (((uintptr_t)_we_allocated_buffer + 32) & ~ ((uintptr_t) (31)));
			memset(_pfbtft, 0, CBALLOC);	
		}
		_use_fbtft = 1;
		clearChangedRange();	// make sure the dirty range is updated.
	} else 
		_use_fbtft = 0;

	return _use_fbtft;	
	#else
	return 0;
	#endif
}

void HX8357_t3n::freeFrameBuffer(void)						// explicit call to release the buffer
{
	#ifdef ENABLE_HX8357_FRAMEBUFFER
	if (_we_allocated_buffer) {
		free(_we_allocated_buffer);
		_pfbtft = NULL;
		_use_fbtft = 0;	// make sure the use is turned off
		_we_allocated_buffer = NULL;
	}
	#endif
}
void HX8357_t3n::updateScreen(void)					// call to say update the screen now.
{
	// Not sure if better here to check flag or check existence of buffer.
	// Will go by buffer as maybe can do interesting things?
	#ifdef ENABLE_HX8357_FRAMEBUFFER
	if (_use_fbtft) {
		beginSPITransaction(_SPI_CLOCK);
		if (_standard && !_updateChangedAreasOnly) {
			// Doing full window. 
			setAddr(0, 0, _width-1, _height-1);
			writecommand_cont(HX8357_RAMWR);

			// BUGBUG doing as one shot.  Not sure if should or not or do like
			// main code and break up into transactions...
			uint16_t *pfbtft_end = &_pfbtft[(HX8357_TFTWIDTH*HX8357_TFTHEIGHT)-1];	// setup 
			uint16_t *pftbft = _pfbtft;

			// Quick write out the data;
			while (pftbft < pfbtft_end) {
				writedata16_cont(*pftbft++);
			}
			writedata16_last(*pftbft);
		} else {
			// setup just to output the clip rectangle area anded with updated area if enabled
			int16_t start_x = _displayclipx1;
			int16_t start_y = _displayclipy1;
			int16_t end_x = _displayclipx2 - 1; 
			int16_t end_y = _displayclipy2 - 1;

			if (_updateChangedAreasOnly) {
				// maybe update range of values to update...
	 			if (_changed_min_x > start_x) start_x = _changed_min_x;
	 			if (_changed_min_y > start_y) start_y = _changed_min_y;
	 			if (_changed_max_x < end_x) end_x = _changed_max_x;
	 			if (_changed_max_y < end_y) end_y = _changed_max_y;
			}

			// Only do if actual area to update
			if ((start_x <= end_x) && (start_y <= end_y)) {
				setAddr(start_x, start_y, end_x, end_y);
				writecommand_cont(HX8357_RAMWR);

				// BUGBUG doing as one shot.  Not sure if should or not or do like
				// main code and break up into transactions...
				uint16_t * pfbPixel_row = &_pfbtft[ start_y*_width + start_x];
				for (uint16_t y = start_y; y <= end_y; y++) {
					uint16_t * pfbPixel = pfbPixel_row;
					for (uint16_t x = start_x; x < end_x; x++) {
						writedata16_cont(*pfbPixel++);
					}
					if (y < (end_y))
						writedata16_cont(*pfbPixel);
					else	
						writedata16_last(*pfbPixel);
					pfbPixel_row += _width;	// setup for the next row. 
				}
			}
		}
		endSPITransaction();
	}
	clearChangedRange();	// make sure the dirty range is updated.	
	#endif
}			 

#ifdef DEBUG_ASYNC_UPDATE
void dumpDMA_TCD(DMABaseClass *dmabc)
{
	Serial.printf("%x %x:", (uint32_t)dmabc, (uint32_t)dmabc->TCD);

	Serial.printf("SA:%x SO:%d AT:%x NB:%x SL:%d DA:%x DO: %d CI:%x DL:%x CS:%x BI:%x\n", (uint32_t)dmabc->TCD->SADDR,
		dmabc->TCD->SOFF, dmabc->TCD->ATTR, dmabc->TCD->NBYTES, dmabc->TCD->SLAST, (uint32_t)dmabc->TCD->DADDR, 
		dmabc->TCD->DOFF, dmabc->TCD->CITER, dmabc->TCD->DLASTSGA, dmabc->TCD->CSR, dmabc->TCD->BITER);
}
#endif

#ifdef ENABLE_HX8357_FRAMEBUFFER
//==============================================
#ifdef ENABLE_HX8357_FRAMEBUFFER
void	HX8357_t3n::initDMASettings(void) 
{
	// Serial4.printf("initDMASettings called %d\n", _dma_state);
	if (_dma_state & HX8357_DMA_INIT) {  // should test for init, but...
		return;	// we already init this. 
	}

	//Serial.println("InitDMASettings");
	uint8_t dmaTXevent = _spi_hardware->tx_dma_channel;
#if defined(__MK66FX1M0__) 
	// T3.6

	// BUGBUG:: check for -1 as wont work on SPI2 on T3.5
//	uint16_t *fbtft_start_dma_addr = _pfbtft;

	
	//Serial.printf("CWW: %d %d %d\n", CBALLOC, SCREEN_DMA_NUM_SETTINGS, count_words_write);
	// Now lets setup DMA access to this memory... 
	_dmasettings[0].sourceBuffer(&_pfbtft[1], (COUNT_WORDS_WRITE-1)*2);
	_dmasettings[0].destination(_pkinetisk_spi->PUSHR);

	// Hack to reset the destination to only output 2 bytes.
	_dmasettings[0].TCD->ATTR_DST = 1;
	_dmasettings[0].replaceSettingsOnCompletion(_dmasettings[1]);

	_dmasettings[1].sourceBuffer(&_pfbtft[COUNT_WORDS_WRITE], COUNT_WORDS_WRITE*2);
	_dmasettings[1].destination(_pkinetisk_spi->PUSHR);
	_dmasettings[1].TCD->ATTR_DST = 1;
	_dmasettings[1].replaceSettingsOnCompletion(_dmasettings[2]);

	_dmasettings[2].sourceBuffer(&_pfbtft[COUNT_WORDS_WRITE*2], COUNT_WORDS_WRITE*2);
	_dmasettings[2].destination(_pkinetisk_spi->PUSHR);
	_dmasettings[2].TCD->ATTR_DST = 1;
	_dmasettings[2].replaceSettingsOnCompletion(_dmasettings[3]);

	// Sort of hack - but wrap around to output the first word again. 
	_dmasettings[3].sourceBuffer(_pfbtft, 2);
	_dmasettings[3].destination(_pkinetisk_spi->PUSHR);
	_dmasettings[3].TCD->ATTR_DST = 1;
	_dmasettings[3].replaceSettingsOnCompletion(_dmasettings[0]);

	// Setup DMA main object
	//Serial.println("Setup _dmatx");
	_dmatx.begin(true);
	_dmatx.triggerAtHardwareEvent(dmaTXevent);
	_dmatx = _dmasettings[0];
	_dmatx.attachInterrupt(dmaInterrupt);
#elif defined(__IMXRT1052__) || defined(__IMXRT1062__)  // Teensy 4.x
	// See if moving the frame buffer to other memory that is not cached helps out
	// to remove tearing and the like...I know with 256 it will be either 256 or 248...
	#if defined(TRY_FULL_DMA_CHAIN)

	// 320*480/5 = 30720
	_dmasettings[0].sourceBuffer(_pfbtft, (COUNT_WORDS_WRITE)*2);
	_dmasettings[0].destination(_pimxrt_spi->TDR);
	_dmasettings[0].TCD->ATTR_DST = 1;
	_dmasettings[0].replaceSettingsOnCompletion(_dmasettings[1]);

	_dmasettings[1].sourceBuffer(&_pfbtft[COUNT_WORDS_WRITE], COUNT_WORDS_WRITE*2);
	_dmasettings[1].destination(_pimxrt_spi->TDR);
	_dmasettings[1].TCD->ATTR_DST = 1;
	_dmasettings[1].replaceSettingsOnCompletion(_dmasettings[2]);

	_dmasettings[2].sourceBuffer(&_pfbtft[COUNT_WORDS_WRITE*2], COUNT_WORDS_WRITE*2);
	_dmasettings[2].destination(_pimxrt_spi->TDR);
	_dmasettings[2].TCD->ATTR_DST = 1;
	_dmasettings[2].replaceSettingsOnCompletion(_dmasettings[3]);

	_dmasettings[3].sourceBuffer(&_pfbtft[COUNT_WORDS_WRITE*3], COUNT_WORDS_WRITE*2);
	_dmasettings[3].destination(_pimxrt_spi->TDR);
	_dmasettings[3].TCD->ATTR_DST = 1;
	_dmasettings[3].replaceSettingsOnCompletion(_dmasettings[4]);

	_dmasettings[4].sourceBuffer(&_pfbtft[COUNT_WORDS_WRITE*4], COUNT_WORDS_WRITE*2);
	_dmasettings[4].destination(_pimxrt_spi->TDR);
	_dmasettings[4].TCD->ATTR_DST = 1;
	_dmasettings[4].replaceSettingsOnCompletion(_dmasettings[0]);
	_dmasettings[4].interruptAtCompletion();

	#else
	_dma_buffer_size = DMA_BUFFER_SIZE;
	_dma_cnt_sub_frames_per_frame = (_count_pixels) / _dma_buffer_size;
	while ((_dma_cnt_sub_frames_per_frame * _dma_buffer_size) != (_count_pixels)) {
		_dma_buffer_size--;
		_dma_cnt_sub_frames_per_frame = (_count_pixels) / _dma_buffer_size;		
	}

	Serial.printf("DMA Init buf size: %d sub frames:%d\n", _dma_buffer_size, _dma_cnt_sub_frames_per_frame);

	_dmasettings[0].sourceBuffer(_dma_buffer1, _dma_buffer_size*2);
	_dmasettings[0].destination(_pimxrt_spi->TDR);
	_dmasettings[0].TCD->ATTR_DST = 1;
	_dmasettings[0].replaceSettingsOnCompletion(_dmasettings[1]);
	_dmasettings[0].interruptAtCompletion();

	_dmasettings[1].sourceBuffer(_dma_buffer2, _dma_buffer_size*2);
	_dmasettings[1].destination(_pimxrt_spi->TDR);
	_dmasettings[1].TCD->ATTR_DST = 1;
	_dmasettings[1].replaceSettingsOnCompletion(_dmasettings[0]);
	_dmasettings[1].interruptAtCompletion();
	#endif
	// Setup DMA main object
	//Serial.println("Setup _dmatx");
	// Serial.println("DMA initDMASettings - before dmatx");
	_dmatx.begin(true);
	_dmatx.triggerAtHardwareEvent(dmaTXevent);
	_dmatx = _dmasettings[0];
	if (_spi_num == 0) _dmatx.attachInterrupt(dmaInterrupt);
	else if (_spi_num == 1) _dmatx.attachInterrupt(dmaInterrupt1);
	else _dmatx.attachInterrupt(dmaInterrupt2);
#else
	// T3.5
	// Lets setup the write size.  For SPI we can use up to 32767 so same size as we use on T3.6...
	// But SPI1 and SPI2 max of 511.  We will use 480 in that case as even divider...

	_dmarx.disable();
	_dmarx.source(_pkinetisk_spi->POPR);
	_dmarx.TCD->ATTR_SRC = 1;
	_dmarx.destination(_dma_dummy_rx);
	_dmarx.disableOnCompletion();
	_dmarx.triggerAtHardwareEvent( _spi_hardware->rx_dma_channel);
	_dmarx.attachInterrupt(dmaInterrupt);
	_dmarx.interruptAtCompletion();

	// We may be using settings chain here so lets set it up. 
	// Now lets setup TX chain.  Note if trigger TX is not set
	// we need to have the RX do it for us.
	_dmatx.disable();
	_dmatx.destination(_pkinetisk_spi->PUSHR);
	_dmatx.TCD->ATTR_DST = 1;
	_dmatx.disableOnCompletion();
	// Current SPIN, has both RX/TX same for SPI1/2 so just know f
	if (_spi_num == 0) {
		_dmatx.triggerAtHardwareEvent(dmaTXevent);
		_dma_write_size_words = COUNT_WORDS_WRITE;
	} else {
		_dma_write_size_words = 480;
	    _dmatx.triggerAtTransfersOf(_dmarx);
	}
	//Serial.printf("Init DMA Settings: TX:%d size:%d\n", dmaTXevent, _dma_write_size_words);

#endif
	_dma_state = HX8357_DMA_INIT;  // Should be first thing set!
	// Serial4.println("DMA initDMASettings - end");

}
#endif

void HX8357_t3n::dumpDMASettings() {
#ifdef DEBUG_ASYNC_UPDATE
#if defined(__MK66FX1M0__) 
	// T3.6
	Serial.printf("DMA dump TCDs %d\n", _dmatx.channel);
	dumpDMA_TCD(&_dmatx);
	dumpDMA_TCD(&_dmasettings[0]);
	dumpDMA_TCD(&_dmasettings[1]);
	dumpDMA_TCD(&_dmasettings[2]);
	dumpDMA_TCD(&_dmasettings[3]);
#elif defined(__IMXRT1052__) || defined(__IMXRT1062__)  // Teensy 4.x
	// Serial4.printf("DMA dump TCDs %d\n", _dmatx.channel);
	dumpDMA_TCD(&_dmatx);
	dumpDMA_TCD(&_dmasettings[0]);
	dumpDMA_TCD(&_dmasettings[1]);
	#if defined(TRY_FULL_DMA_CHAIN)
	dumpDMA_TCD(&_dmasettings[2]);
	dumpDMA_TCD(&_dmasettings[3]);
	dumpDMA_TCD(&_dmasettings[4]);
	#endif
#else
	Serial.printf("DMA dump TX:%d RX:%d\n", _dmatx.channel, _dmarx.channel);
	dumpDMA_TCD(&_dmatx);
	dumpDMA_TCD(&_dmarx);
#endif	
#endif

}

bool HX8357_t3n::updateScreenAsync(bool update_cont)					// call to say update the screen now.
{
	// Not sure if better here to check flag or check existence of buffer.
	// Will go by buffer as maybe can do interesting things?
	// BUGBUG:: only handles full screen so bail on the rest of it...
	#ifdef ENABLE_HX8357_FRAMEBUFFER
	if (!_use_fbtft) return false;


	#if defined(__MK64FX512__)  // If T3.5 only allow on SPI...
	// The T3.5 DMA to SPI has issues with preserving stuff like we want 16 bit mode
	// and we want CS to stay on... So hack it.  We will turn off using CS for the CS
	//	pin.
	if (!_csport) {
		pcs_data = 0;
		pcs_command = pcs_data | _pspi->setCS(_dc);
		pinMode(_cs, OUTPUT);
		_csport    = portOutputRegister(digitalPinToPort(_cs));
		_cspinmask = digitalPinToBitMask(_cs);
		*_csport |= _cspinmask;
	}
	#endif

#ifdef DEBUG_ASYNC_LEDS
	digitalWriteFast(DEBUG_PIN_1, HIGH);
#endif
	// Init DMA settings. 
	initDMASettings();

	// Don't start one if already active.
	if (_dma_state & HX8357_DMA_ACTIVE) {
	#ifdef DEBUG_ASYNC_LEDS
		digitalWriteFast(DEBUG_PIN_1, LOW);
	#endif
		return false;
	}

#if defined(__MK66FX1M0__) 
	//==========================================
	// T3.6
	//==========================================
	if (update_cont) {
		// Try to link in #3 into the chain
		_dmasettings[2].replaceSettingsOnCompletion(_dmasettings[3]);
		_dmasettings[2].TCD->CSR &= ~(DMA_TCD_CSR_INTMAJOR | DMA_TCD_CSR_DREQ);  // Don't interrupt on this one... 
		_dmasettings[3].interruptAtCompletion();
		_dmasettings[3].TCD->CSR &= ~(DMA_TCD_CSR_DREQ);  // Don't disable on this one  
		_dma_state |= HX8357_DMA_CONT;
	} else {
		// In this case we will only run through once...
		_dmasettings[2].replaceSettingsOnCompletion(_dmasettings[0]);
		_dmasettings[2].interruptAtCompletion();
		_dmasettings[2].disableOnCompletion();
		_dma_state &= ~HX8357_DMA_CONT;
	}


#ifdef DEBUG_ASYNC_UPDATE
	dumpDMASettings();
#endif
	beginSPITransaction(_SPI_CLOCK);

	// Doing full window. 
	setAddr(0, 0, _width-1, _height-1);
	writecommand_cont(HX8357_RAMWR);

	// Write the first Word out before enter DMA as to setup the proper CS/DC/Continue flaugs
	writedata16_cont(*_pfbtft);
	// now lets start up the DMA
//	volatile uint16_t  biter = _dmatx.TCD->BITER;
	//DMA_CDNE_CDNE(_dmatx.channel);
//	_dmatx = _dmasettings[0];
//	_dmatx.TCD->BITER = biter;
	_dma_frame_count = 0;  // Set frame count back to zero. 
	_dmaActiveDisplay = this;
	_dma_state |= HX8357_DMA_ACTIVE;
	_pkinetisk_spi->RSER |= SPI_RSER_TFFF_DIRS |	 SPI_RSER_TFFF_RE;	 // Set DMA Interrupt Request Select and Enable register
	_pkinetisk_spi->MCR &= ~SPI_MCR_HALT;  //Start transfers.
	_dmatx.enable();
	//==========================================
	// T4
	//==========================================
#elif defined(__IMXRT1052__) || defined(__IMXRT1062__)  // Teensy 4.x
	#if defined(TRY_FULL_DMA_CHAIN)
	/////////////////////////////
	// BUGBUG try first not worry about continueous or not.
  	// Start off remove disable on completion from both...
	// it will be the ISR that disables it... 
	if ((uint32_t)_pfbtft >= 0x20200000u)  arm_dcache_flush(_pfbtft, CBALLOC);

	_dmasettings[4].TCD->CSR &= ~( DMA_TCD_CSR_DREQ);
	beginSPITransaction(_SPI_CLOCK);
	// Doing full window. 
	setAddr(0, 0, _width-1, _height-1);
	writecommand_last(HX8357_RAMWR);

	// Update TCR to 16 bit mode. and output the first entry.
	_spi_fcr_save = _pimxrt_spi->FCR;	// remember the FCR
	_pimxrt_spi->FCR = 0;	// clear water marks... 	
	maybeUpdateTCR(_tcr_dc_not_assert | LPSPI_TCR_FRAMESZ(15) | LPSPI_TCR_RXMSK /*| LPSPI_TCR_CONT*/);
 	_pimxrt_spi->DER = LPSPI_DER_TDDE;
	_pimxrt_spi->SR = 0x3f00;	// clear out all of the other status...

  	_dmatx.triggerAtHardwareEvent( _spi_hardware->tx_dma_channel );

 	_dmatx = _dmasettings[0];

  	_dmatx.begin(false);
  	_dmatx.enable();

#ifdef DEBUG_ASYNC_UPDATE
	dumpDMASettings();
#endif

	_dma_frame_count = 0;  // Set frame count back to zero. 
	_dmaActiveDisplay[_spi_num]  = this;
	if (update_cont) {
		_dma_state |= HX8357_DMA_CONT;
	} else {
		_dmasettings[4].disableOnCompletion();
		_dma_state &= ~HX8357_DMA_CONT;
	}

	_dma_state |= HX8357_DMA_ACTIVE;

	////////////////////////////
	#else
  	// Start off remove disable on completion from both...
	// it will be the ISR that disables it... 
	_dmasettings[0].TCD->CSR &= ~( DMA_TCD_CSR_DREQ);
	_dmasettings[1].TCD->CSR &= ~( DMA_TCD_CSR_DREQ);

#ifdef DEBUG_ASYNC_UPDATE
	dumpDMASettings();
#endif
	// Lets copy first parts of frame buffer into our two sub-frames
	_pfbtft_async = _pfbtft;		// remember buffer pointer at start of operation, may allow user to swap...
	memcpy(_dma_buffer1, _pfbtft_async, _dma_buffer_size*2);
	memcpy(_dma_buffer2, &_pfbtft_async[_dma_buffer_size], _dma_buffer_size*2);
	_dma_pixel_index = _dma_buffer_size*2;
	_dma_sub_frame_count = 0;	// 

	beginSPITransaction(_SPI_CLOCK);
	// Doing full window. 
	setAddr(0, 0, _width-1, _height-1);
	writecommand_last(HX8357_RAMWR);

	// Update TCR to 16 bit mode. and output the first entry.
	_spi_fcr_save = _pimxrt_spi->FCR;	// remember the FCR
	_pimxrt_spi->FCR = 0;	// clear water marks... 	
	maybeUpdateTCR(_tcr_dc_not_assert | LPSPI_TCR_FRAMESZ(15) | LPSPI_TCR_RXMSK /*| LPSPI_TCR_CONT*/);
 	_pimxrt_spi->DER = LPSPI_DER_TDDE;
	_pimxrt_spi->SR = 0x3f00;	// clear out all of the other status...

  	_dmatx.triggerAtHardwareEvent( _spi_hardware->tx_dma_channel );

 	_dmatx = _dmasettings[0];

  	_dmatx.begin(false);
  	_dmatx.enable();

	_dma_frame_count = 0;  // Set frame count back to zero. 
	_dmaActiveDisplay[_spi_num]  = this;
	if (update_cont) {
		_dma_state |= HX8357_DMA_CONT;
	} else {
		_dma_state &= ~HX8357_DMA_CONT;

	}

	_dma_state |= HX8357_DMA_ACTIVE;
	#endif
#else
	//==========================================
	// T3.5
	//==========================================

	// lets setup the initial pointers. 
	_dmatx.sourceBuffer(&_pfbtft[1], (_dma_write_size_words-1)*2);
	_dmatx.TCD->SLAST = 0;	// Finish with it pointing to next location
	_dmarx.transferCount(_dma_write_size_words);
	_dma_count_remaining = CBALLOC/2 - _dma_write_size_words;	// how much more to transfer? 
	//Serial.printf("SPI1/2 - TC:%d TR:%d\n", _dma_write_size_words, _dma_count_remaining);

#ifdef DEBUG_ASYNC_UPDATE
	dumpDMASettings();
#endif

	beginSPITransaction(_SPI_CLOCK);
	// Doing full window. 
	setAddr(0, 0, _width-1, _height-1);
	writecommand_cont(HX8357_RAMWR);

	// Write the first Word out before enter DMA as to setup the proper CS/DC/Continue flaugs
	// On T3.5 DMA only appears to work with CTAR 0 so hack it up...
	_pkinetisk_spi->CTAR0 |= SPI_CTAR_FMSZ(8); 	// Hack convert from 8 bit to 16 bit...

	_pkinetisk_spi->MCR = SPI_MCR_MSTR | SPI_MCR_CLR_RXF | SPI_MCR_PCSIS(0x1F);

	_pkinetisk_spi->SR = 0xFF0F0000;

	// Lets try to output the first byte to make sure that we are in 16 bit mode...
	_pkinetisk_spi->PUSHR = *_pfbtft | SPI_PUSHR_CTAS(0) | SPI_PUSHR_CONT;	

	if (_spi_num == 0) {
		// SPI - has both TX and RX so use it
		_pkinetisk_spi->RSER =  SPI_RSER_RFDF_RE | SPI_RSER_RFDF_DIRS | SPI_RSER_TFFF_RE | SPI_RSER_TFFF_DIRS;

	    _dmarx.enable();
	    _dmatx.enable();
	} else {
		_pkinetisk_spi->RSER =  SPI_RSER_RFDF_RE | SPI_RSER_RFDF_DIRS ;
	    _dmatx.triggerAtTransfersOf(_dmarx);
	    _dmatx.enable();
	    _dmarx.enable();
	}

	_dma_frame_count = 0;  // Set frame count back to zero. 
	_dmaActiveDisplay = this;
	if (update_cont) {
		_dma_state |= HX8357_DMA_CONT;
	} else {
		_dma_state &= ~HX8357_DMA_CONT;

	}

	_dma_state |= HX8357_DMA_ACTIVE;
#endif	
#ifdef DEBUG_ASYNC_LEDS
	digitalWriteFast(DEBUG_PIN_1, LOW);
#endif
	return true;
    #else
    return false;     // no frame buffer so will never start... 
	#endif

}			 

void HX8357_t3n::endUpdateAsync() {
	// make sure it is on
	#ifdef ENABLE_HX8357_FRAMEBUFFER
	if (_dma_state & HX8357_DMA_CONT) {
		_dma_state &= ~HX8357_DMA_CONT; // Turn of the continueous mode
		#if defined(TRY_FULL_DMA_CHAIN)
		_dmasettings[4].disableOnCompletion();
		//Serial.println(">>> disable on completion set");
		#endif	
	}
	#endif
}
	
void HX8357_t3n::waitUpdateAsyncComplete(void) 
{
	#ifdef ENABLE_HX8357_FRAMEBUFFER
#ifdef DEBUG_ASYNC_LEDS
	digitalWriteFast(DEBUG_PIN_3, HIGH);
#endif

	while ((_dma_state & HX8357_DMA_ACTIVE)) {
		// asm volatile("wfi");
	};
#ifdef DEBUG_ASYNC_LEDS
	digitalWriteFast(DEBUG_PIN_3, LOW);
#endif
	#endif	
}
#endif
//=======================================================================


void HX8357_t3n::setAddrWindow(uint16_t x0, uint16_t y0, uint16_t x1, uint16_t y1)
{
	beginSPITransaction(_SPI_CLOCK);
	setAddr(x0, y0, x1, y1);
	writecommand_last(HX8357_RAMWR); // write to RAM
	endSPITransaction();
}

void HX8357_t3n::pushColor(uint16_t color)
{
	beginSPITransaction(_SPI_CLOCK);
	writedata16_last(color);
	endSPITransaction();
}

void HX8357_t3n::drawPixel(int16_t x, int16_t y, uint16_t color) {
	x += _originx;
	y += _originy;
	if((x < _displayclipx1) ||(x >= _displayclipx2) || (y < _displayclipy1) || (y >= _displayclipy2)) return;

	#ifdef ENABLE_HX8357_FRAMEBUFFER
	if (_use_fbtft) {
		updateChangedRange(x, y);		// update the range of the screen that has been changed;
		_pfbtft[y*_width + x] = color;

	} else 
	#endif
	{
		beginSPITransaction(_SPI_CLOCK);
		setAddr(x, y, x, y);
		writecommand_cont(HX8357_RAMWR);
		writedata16_last(color);
		endSPITransaction();
	}
}

void HX8357_t3n::drawFastVLine(int16_t x, int16_t y, int16_t h, uint16_t color)
{
	x+=_originx;
	y+=_originy;
	// Rectangular clipping
	if((x < _displayclipx1) || (x >= _displayclipx2) || (y >= _displayclipy2)) return;
	if(y < _displayclipy1) { h = h - (_displayclipy1 - y); y = _displayclipy1;}
	if((y+h-1) >= _displayclipy2) h = _displayclipy2-y;
	if(h<1) return;

	#ifdef ENABLE_HX8357_FRAMEBUFFER
	if (_use_fbtft) {
		updateChangedRange(x, y, 1, h);		// update the range of the screen that has been changed;
		uint16_t * pfbPixel = &_pfbtft[ y*_width + x];
		while (h--) {
			*pfbPixel = color;
			pfbPixel += _width;
		}
	} else 
	#endif
	{
		beginSPITransaction(_SPI_CLOCK);
		setAddr(x, y, x, y+h-1);
		writecommand_cont(HX8357_RAMWR);
		while (h-- > 1) {
			writedata16_cont(color);
		}
		writedata16_last(color);
		endSPITransaction();
	}
}

void HX8357_t3n::drawFastHLine(int16_t x, int16_t y, int16_t w, uint16_t color)
{
	x+=_originx;
	y+=_originy;

	// Rectangular clipping
	if((y < _displayclipy1) || (x >= _displayclipx2) || (y >= _displayclipy2)) return;
	if(x<_displayclipx1) { w = w - (_displayclipx1 - x); x = _displayclipx1; }
	if((x+w-1) >= _displayclipx2)  w = _displayclipx2-x;
	if (w<1) return;

	#ifdef ENABLE_HX8357_FRAMEBUFFER
	if (_use_fbtft) {
		updateChangedRange(x, y, w, 1);		// update the range of the screen that has been changed;
		if ((x&1) || (w&1)) {
			uint16_t * pfbPixel = &_pfbtft[ y*_width + x];
			while (w--) {
				*pfbPixel++ = color;
			}
		} else {
			// X is even and so is w, try 32 bit writes..
			uint32_t color32 = (color << 16) | color;
			uint32_t * pfbPixel = (uint32_t*)((uint16_t*)&_pfbtft[ y*_width + x]);
			while (w) {
				*pfbPixel++ = color32;
				w -= 2;
			}
		}
	} else 
	#endif
	{
		beginSPITransaction(_SPI_CLOCK);
		setAddr(x, y, x+w-1, y);
		writecommand_cont(HX8357_RAMWR);
		while (w-- > 1) {
			writedata16_cont(color);
		}
		writedata16_last(color);
		endSPITransaction();
	}
}

void HX8357_t3n::fillScreen(uint16_t color)
{
	#ifdef ENABLE_HX8357_FRAMEBUFFER
	if (_use_fbtft && _standard) {
		// Speed up lifted from Franks DMA code... _standard is if no offsets and rects..
		updateChangedRange(0, 0, _width, _height);		// update the range of the screen that has been changed;
		uint32_t color32 = (color << 16) | color;

		uint32_t *pfbPixel = (uint32_t *)_pfbtft;
		uint32_t *pfbtft_end = (uint32_t *)((uint16_t *)&_pfbtft[(HX8357_TFTWIDTH * HX8357_TFTHEIGHT)]); // setup
		while (pfbPixel < pfbtft_end) {
			*pfbPixel++ = color32; *pfbPixel++ = color32; *pfbPixel++ = color32;*pfbPixel++ = color32;
			*pfbPixel++ = color32; *pfbPixel++ = color32; *pfbPixel++ = color32;*pfbPixel++ = color32;
			*pfbPixel++ = color32; *pfbPixel++ = color32; *pfbPixel++ = color32;*pfbPixel++ = color32;
			*pfbPixel++ = color32; *pfbPixel++ = color32; *pfbPixel++ = color32;*pfbPixel++ = color32;
			*pfbPixel++ = color32; *pfbPixel++ = color32; *pfbPixel++ = color32;*pfbPixel++ = color32;
			*pfbPixel++ = color32; *pfbPixel++ = color32; *pfbPixel++ = color32;*pfbPixel++ = color32;
			*pfbPixel++ = color32; *pfbPixel++ = color32; *pfbPixel++ = color32;*pfbPixel++ = color32;
			*pfbPixel++ = color32; *pfbPixel++ = color32; *pfbPixel++ = color32;*pfbPixel++ = color32;
		}

	} else 
	#endif
	{
		fillRect(0, 0, _width, _height, color);
	}
}

// fill a rectangle
void HX8357_t3n::fillRect(int16_t x, int16_t y, int16_t w, int16_t h, uint16_t color)
{
	x+=_originx;
	y+=_originy;

	// Rectangular clipping (drawChar w/big text requires this)
	if((x >= _displayclipx2) || (y >= _displayclipy2)) return;
	if (((x+w) <= _displayclipx1) || ((y+h) <= _displayclipy1)) return;
	if(x < _displayclipx1) {	w -= (_displayclipx1-x); x = _displayclipx1; 	}
	if(y < _displayclipy1) {	h -= (_displayclipy1 - y); y = _displayclipy1; 	}
	if((x + w - 1) >= _displayclipx2)  w = _displayclipx2  - x;
	if((y + h - 1) >= _displayclipy2) h = _displayclipy2 - y;

	#ifdef ENABLE_HX8357_FRAMEBUFFER
	if (_use_fbtft) {
		updateChangedRange(x, y, w, h);		// update the range of the screen that has been changed;
		if ((x&1) || (w&1)) {
			uint16_t * pfbPixel_row = &_pfbtft[ y*_width + x];
			for (;h>0; h--) {
				uint16_t * pfbPixel = pfbPixel_row;
				for (int i = 0 ;i < w; i++) {
					*pfbPixel++ = color;
				}
				pfbPixel_row += _width;
			}
		} else {
			// Horizontal is even number so try 32 bit writes instead
			uint32_t color32 = (color << 16) | color;
			uint32_t * pfbPixel_row = (uint32_t *)((uint16_t*)&_pfbtft[ y*_width + x]);
			w = w/2;	// only iterate half the times
			for (;h>0; h--) {
				uint32_t * pfbPixel = pfbPixel_row;
				for (int i = 0 ;i < w; i++) {
					*pfbPixel++ = color32;
				}
				pfbPixel_row += (_width/2);
			}
		}
	} else 
	#endif
	{

		// TODO: this can result in a very long transaction time
		// should break this into multiple transactions, even though
		// it'll cost more overhead, so we don't stall other SPI libs
		beginSPITransaction(_SPI_CLOCK);
		setAddr(x, y, x+w-1, y+h-1);
		writecommand_cont(HX8357_RAMWR);
		for(y=h; y>0; y--) {
			for(x=w; x>1; x--) {
				writedata16_cont(color);
			}
			writedata16_last(color);
#if 0
			if (y > 1 && (y & 1)) {
				endSPITransaction();
				beginSPITransaction(_SPI_CLOCK);
			}
#endif			
		}
		endSPITransaction();
	}
}

// fillRectVGradient	- fills area with vertical gradient
void HX8357_t3n::fillRectVGradient(int16_t x, int16_t y, int16_t w, int16_t h, uint16_t color1, uint16_t color2)
{
	x+=_originx;
	y+=_originy;

	// Rectangular clipping 
	if((x >= _displayclipx2) || (y >= _displayclipy2)) return;
	if(x < _displayclipx1) {	w -= (_displayclipx1-x); x = _displayclipx1; 	}
	if(y < _displayclipy1) {	h -= (_displayclipy1 - y); y = _displayclipy1; 	}
	if((x + w - 1) >= _displayclipx2)  w = _displayclipx2  - x;
	if((y + h - 1) >= _displayclipy2) h = _displayclipy2 - y;
	
	int16_t r1, g1, b1, r2, g2, b2, dr, dg, db, r, g, b;
	color565toRGB14(color1,r1,g1,b1);
	color565toRGB14(color2,r2,g2,b2);
	dr=(r2-r1)/h; dg=(g2-g1)/h; db=(b2-b1)/h;
	r=r1;g=g1;b=b1;	

	#ifdef ENABLE_HX8357_FRAMEBUFFER
	if (_use_fbtft) {
		updateChangedRange(x, y, w, h);		// update the range of the screen that has been changed;
		if ((x&1) || (w&1)) {
			uint16_t * pfbPixel_row = &_pfbtft[ y*_width + x];
			for (;h>0; h--) {
				uint16_t color = RGB14tocolor565(r,g,b);
				uint16_t * pfbPixel = pfbPixel_row;
				for (int i = 0 ;i < w; i++) {
					*pfbPixel++ = color;
				}
				r+=dr;g+=dg; b+=db;
				pfbPixel_row += _width;
			}
		} else {
			// Horizontal is even number so try 32 bit writes instead
			uint32_t * pfbPixel_row = (uint32_t *)((uint16_t*)&_pfbtft[ y*_width + x]);
			w = w/2;	// only iterate half the times
			for (;h>0; h--) {
				uint32_t * pfbPixel = pfbPixel_row;
				uint16_t color = RGB14tocolor565(r,g,b);
				uint32_t color32 = (color << 16) | color;
				for (int i = 0 ;i < w; i++) {
					*pfbPixel++ = color32;
				}
				pfbPixel_row += (_width/2);
				r+=dr;g+=dg; b+=db;
			}
		}
	} else 
	#endif
	{		
		beginSPITransaction(_SPI_CLOCK);
		setAddr(x, y, x+w-1, y+h-1);
		writecommand_cont(HX8357_RAMWR);
		for(y=h; y>0; y--) {
			uint16_t color = RGB14tocolor565(r,g,b);

			for(x=w; x>1; x--) {
				writedata16_cont(color);
			}
			writedata16_last(color);
			if (y > 1 && (y & 1)) {
				endSPITransaction();
				beginSPITransaction(_SPI_CLOCK);
			}
			r+=dr;g+=dg; b+=db;
		}
		endSPITransaction();
	}
}

// fillRectHGradient	- fills area with horizontal gradient
void HX8357_t3n::fillRectHGradient(int16_t x, int16_t y, int16_t w, int16_t h, uint16_t color1, uint16_t color2)
{
	x+=_originx;
	y+=_originy;

	// Rectangular clipping 
	if((x >= _displayclipx2) || (y >= _displayclipy2)) return;
	if(x < _displayclipx1) {	w -= (_displayclipx1-x); x = _displayclipx1; 	}
	if(y < _displayclipy1) {	h -= (_displayclipy1 - y); y = _displayclipy1; 	}
	if((x + w - 1) >= _displayclipx2)  w = _displayclipx2  - x;
	if((y + h - 1) >= _displayclipy2) h = _displayclipy2 - y;
	
	int16_t r1, g1, b1, r2, g2, b2, dr, dg, db, r, g, b;
	uint16_t color;
	color565toRGB14(color1,r1,g1,b1);
	color565toRGB14(color2,r2,g2,b2);
	dr=(r2-r1)/w; dg=(g2-g1)/w; db=(b2-b1)/w;
	r=r1;g=g1;b=b1;	
	#ifdef ENABLE_HX8357_FRAMEBUFFER
	if (_use_fbtft) {
		updateChangedRange(x, y, w, h);		// update the range of the screen that has been changed;
		uint16_t * pfbPixel_row = &_pfbtft[ y*_width + x];
		for (;h>0; h--) {
			uint16_t * pfbPixel = pfbPixel_row;
			for (int i = 0 ;i < w; i++) {
				*pfbPixel++ = RGB14tocolor565(r,g,b);
				r+=dr;g+=dg; b+=db;
			}
			pfbPixel_row += _width;
			r=r1;g=g1;b=b1;
		}
	} else 
	#endif
	{
		beginSPITransaction(_SPI_CLOCK);
		setAddr(x, y, x+w-1, y+h-1);
		writecommand_cont(HX8357_RAMWR);
		for(y=h; y>0; y--) {
			for(x=w; x>1; x--) {
				color = RGB14tocolor565(r,g,b);
				writedata16_cont(color);
				r+=dr;g+=dg; b+=db;
			}
			color = RGB14tocolor565(r,g,b);
			writedata16_last(color);
			if (y > 1 && (y & 1)) {
				endSPITransaction();
				beginSPITransaction(_SPI_CLOCK);
			}
			r=r1;g=g1;b=b1;
		}
		endSPITransaction();
	}
}

// fillScreenVGradient - fills screen with vertical gradient
void HX8357_t3n::fillScreenVGradient(uint16_t color1, uint16_t color2)
{
	fillRectVGradient(0,0,_width,_height,color1,color2);
}

// fillScreenHGradient - fills screen with horizontal gradient
void HX8357_t3n::fillScreenHGradient(uint16_t color1, uint16_t color2)
{
	fillRectHGradient(0,0,_width,_height,color1,color2);
}

#define MADCTL_MY  0x80 ///< Bottom to top
#define MADCTL_MX  0x40 ///< Right to left
#define MADCTL_MV  0x20 ///< Reverse Mode
#define MADCTL_ML  0x10 ///< LCD refresh Bottom to top
#define MADCTL_RGB 0x00 ///< Red-Green-Blue pixel order
#define MADCTL_BGR 0x08 ///< Blue-Green-Red pixel order
#define MADCTL_MH  0x04 ///< LCD refresh right to left

void HX8357_t3n::setRotation(uint8_t m)
{
	rotation = m & 3; // can't be higher than 3
	beginSPITransaction(_SPI_CLOCK);
	writecommand_cont(HX8357_MADCTL);
	switch (rotation) {
	case 0:
		writedata8_last(MADCTL_MX | MADCTL_MY | MADCTL_RGB);
		_width  = HX8357_TFTWIDTH;
		_height = HX8357_TFTHEIGHT;
		break;
	case 1:
		writedata8_last(MADCTL_MV | MADCTL_MY | MADCTL_RGB);
		_width  = HX8357_TFTHEIGHT;
		_height = HX8357_TFTWIDTH;
		break;
	case 2:
		writedata8_last(MADCTL_RGB);
		_width  = HX8357_TFTWIDTH;
		_height = HX8357_TFTHEIGHT;
		break;
	case 3:
		writedata8_last(MADCTL_MX | MADCTL_MV | MADCTL_RGB);
		_width  = HX8357_TFTHEIGHT;
		_height = HX8357_TFTWIDTH;
		break;
	}
	endSPITransaction();
	setClipRect();
	setOrigin();
	
	cursor_x = 0;
	cursor_y = 0;
}

void HX8357_t3n::setScroll(uint16_t offset)
{
	beginSPITransaction(_SPI_CLOCK);
	writecommand_cont(HX8357_VSCRSADD);
	writedata16_last(offset);
	endSPITransaction();
}

void HX8357_t3n::invertDisplay(boolean i)
{
	beginSPITransaction(_SPI_CLOCK);
	writecommand_last(i ? HX8357_INVON : HX8357_INVOFF);
	endSPITransaction();
}










/*
uint8_t HX8357_t3n::readdata(void)
{
  uint8_t r;
       // Try to work directly with SPI registers...
       // First wait until output queue is empty
        uint16_t wTimeout = 0xffff;
        while (((_pkinetisk_spi->SR) & (15 << 12)) && (--wTimeout)) ; // wait until empty
        
//       	_pkinetisk_spi->MCR |= SPI_MCR_CLR_RXF; // discard any received data
//		_pkinetisk_spi->SR = SPI_SR_TCF;
        
        // Transfer a 0 out... 
        writedata8_cont(0);   
        
        // Now wait until completed. 
        wTimeout = 0xffff;
        while (((_pkinetisk_spi->SR) & (15 << 12)) && (--wTimeout)) ; // wait until empty
        r = _pkinetisk_spi->POPR;  // get the received byte... should check for it first...
    return r;
}
 */

uint8_t HX8357_t3n::readcommand8(uint8_t c, uint8_t index)
{
    // Bail if not valid miso
    if (_miso == 0xff) return 0;

 #ifdef KINETISK
    uint16_t wTimeout = 0xffff;
    uint8_t r=0;

    beginSPITransaction(_SPI_CLOCK);
	if (_spi_num == 0) {
		// Only SPI object has larger queue
	    while (((_pkinetisk_spi->SR) & (15 << 12)) && (--wTimeout)) ; // wait until empty

	    // Make sure the last frame has been sent...
	    _pkinetisk_spi->SR = SPI_SR_TCF;   // dlear it out;
	    wTimeout = 0xffff;
	    while (!((_pkinetisk_spi->SR) & SPI_SR_TCF) && (--wTimeout)) ; // wait until it says the last frame completed

	    // clear out any current received bytes
	    wTimeout = 0x10;    // should not go more than 4...
	    while ((((_pkinetisk_spi->SR) >> 4) & 0xf) && (--wTimeout))  {
	        r = _pkinetisk_spi->POPR;
	    }

	    //writecommand(0xD9); // sekret command
		_pkinetisk_spi->PUSHR = 0xD9 | (pcs_command << 16) | SPI_PUSHR_CTAS(0) | SPI_PUSHR_CONT;
	//	while (((_pkinetisk_spi->SR) & (15 << 12)) > (3 << 12)) ; // wait if FIFO full

	    // writedata(0x10 + index);
		_pkinetisk_spi->PUSHR = (0x10 + index) | (pcs_data << 16) | SPI_PUSHR_CTAS(0);
	//	while (((_pkinetisk_spi->SR) & (15 << 12)) > (3 << 12)) ; // wait if FIFO full
	    // writecommand(c);
	   	_pkinetisk_spi->PUSHR = c | (pcs_command << 16) | SPI_PUSHR_CTAS(0) | SPI_PUSHR_CONT;
	//	while (((_pkinetisk_spi->SR) & (15 << 12)) > (3 << 12)) ; // wait if FIFO full

	    // readdata
		_pkinetisk_spi->PUSHR = 0 | (pcs_data << 16) | SPI_PUSHR_CTAS(0);
	//	while (((_pkinetisk_spi->SR) & (15 << 12)) > (3 << 12)) ; // wait if FIFO full

	    // Now wait until completed.
	    wTimeout = 0xffff;
	    while (((_pkinetisk_spi->SR) & (15 << 12)) && (--wTimeout)) ; // wait until empty

	    // Make sure the last frame has been sent...
	    _pkinetisk_spi->SR = SPI_SR_TCF;   // dlear it out;
	    wTimeout = 0xffff;
	    while (!((_pkinetisk_spi->SR) & SPI_SR_TCF) && (--wTimeout)) ; // wait until it says the last frame completed

	    wTimeout = 0x10;    // should not go more than 4...
	    // lets get all of the values on the FIFO
	    while ((((_pkinetisk_spi->SR) >> 4) & 0xf) && (--wTimeout))  {
	        r = _pkinetisk_spi->POPR;
	    }
	} else {
		while (((_pkinetisk_spi->SR) & (15 << 12)) && (--wTimeout)) ; // wait until empty

	    // Make sure the last frame has been sent...
	    _pkinetisk_spi->SR = SPI_SR_TCF;   // dlear it out;
	    wTimeout = 0xffff;
	    while (!((_pkinetisk_spi->SR) & SPI_SR_TCF) && (--wTimeout)) ; // wait until it says the last frame completed

	    // clear out any current received bytes
	    wTimeout = 0x10;    // should not go more than 4...
	    while ((((_pkinetisk_spi->SR) >> 4) & 0xf) && (--wTimeout))  {
	        r = _pkinetisk_spi->POPR;
	    }

	    //writecommand(0xD9); // sekret command
		_pkinetisk_spi->PUSHR = 0xD9 | (pcs_command << 16) | SPI_PUSHR_CTAS(0) | SPI_PUSHR_CONT;
		while (((_pkinetisk_spi->SR) & (15 << 12)) > (0 << 12)) ; // wait if FIFO full

	    // writedata(0x10 + index);
		_pkinetisk_spi->PUSHR = (0x10 + index) | (pcs_data << 16) | SPI_PUSHR_CTAS(0);
		while (((_pkinetisk_spi->SR) & (15 << 12)) > (0 << 12)) ; // wait if FIFO full

		// See if there are any return values to pop 
	    while (((_pkinetisk_spi->SR) >> 4) & 0xf)  {
	        r = _pkinetisk_spi->POPR;
	    }

	    // writecommand(c);
	   	_pkinetisk_spi->PUSHR = c | (pcs_command << 16) | SPI_PUSHR_CTAS(0) | SPI_PUSHR_CONT;
		while (((_pkinetisk_spi->SR) & (15 << 12)) > (0 << 12)) ; // wait if FIFO full

		// See if there are any return values to pop 
	    while (((_pkinetisk_spi->SR) >> 4) & 0xf)  {
	        r = _pkinetisk_spi->POPR;
	    }

	    // readdata
		_pkinetisk_spi->PUSHR = 0 | (pcs_data << 16) | SPI_PUSHR_CTAS(0);
		while (((_pkinetisk_spi->SR) & (15 << 12)) > (0 << 12)) ; // wait if FIFO full

		// See if there are any return values to pop 
	    while (((_pkinetisk_spi->SR) >> 4) & 0xf)  {
	        r = _pkinetisk_spi->POPR;
	    }
	    // Now wait until completed.
	    wTimeout = 0xffff;
	    while (((_pkinetisk_spi->SR) & (15 << 12)) && (--wTimeout)) ; // wait until empty

	    // Make sure the last frame has been sent...
	    _pkinetisk_spi->SR = SPI_SR_TCF;   // dlear it out;
	    wTimeout = 0xffff;
	    while (!((_pkinetisk_spi->SR) & SPI_SR_TCF) && (--wTimeout)) ; // wait until it says the last frame completed

	    wTimeout = 0x10;    // should not go more than 4...
	    // lets get all of the values on the FIFO
	    while ((((_pkinetisk_spi->SR) >> 4) & 0xf) && (--wTimeout))  {
	        r = _pkinetisk_spi->POPR;
	    }

	}  
    endSPITransaction();
    return r;  // get the received byte... should check for it first...
#elif defined(__IMXRT1052__) || defined(__IMXRT1062__)  // Teensy 4.x 
    uint16_t wTimeout = 0xffff;
    uint8_t r=0;

    beginSPITransaction(_SPI_CLOCK_READ);
    // Lets assume that queues are empty as we just started transaction.
	_pimxrt_spi->CR = LPSPI_CR_MEN | LPSPI_CR_RRF /* | LPSPI_CR_RTF */;   // actually clear both...
    //writecommand(0xD9); // sekret command
    maybeUpdateTCR(_tcr_dc_assert | LPSPI_TCR_FRAMESZ(7) | LPSPI_TCR_CONT);
	_pimxrt_spi->TDR = 0xD9;

    // writedata(0x10 + index);
	maybeUpdateTCR(_tcr_dc_not_assert | LPSPI_TCR_FRAMESZ(7) | LPSPI_TCR_CONT);
	_pimxrt_spi->TDR = 0x10 + index;

    // writecommand(c);
    maybeUpdateTCR(_tcr_dc_assert | LPSPI_TCR_FRAMESZ(7) | LPSPI_TCR_CONT);
	_pimxrt_spi->TDR = c;

    // readdata
	maybeUpdateTCR(_tcr_dc_not_assert | LPSPI_TCR_FRAMESZ(7));
	_pimxrt_spi->TDR = 0;

    // Now wait until completed.
    wTimeout = 0xffff;
    uint8_t rx_count = 4;
    while (rx_count && wTimeout) {
        if ((_pimxrt_spi->RSR & LPSPI_RSR_RXEMPTY) == 0)  {
            r =_pimxrt_spi->RDR;  // Read any pending RX bytes in
            rx_count--; //decrement count of bytes still levt
        }
    }
    endSPITransaction();
    return r;  // get the received byte... should check for it first...
#else
	beginSPITransaction(_SPI_CLOCK);
	writecommand_cont(0xD9);
	writedata8_cont(0x10 + index);

	writecommand_cont(c);
	writedata8_cont(0);
	uint8_t r = waitTransmitCompleteReturnLast();
	endSPITransaction();
	return r;

#endif   
}

// Read Pixel at x,y and get back 16-bit packed color
#define READ_PIXEL_PUSH_BYTE 0x3f
uint16_t HX8357_t3n::readPixel(int16_t x, int16_t y)
{
#ifdef KINETISK	
	//BUGBUG:: Should add some validation of X and Y
	// Now if we are in buffer mode can return real fast
	#ifdef ENABLE_HX8357_FRAMEBUFFER
	if (_use_fbtft) {
		x+=_originx;
		y+=_originy;

		return _pfbtft[y*_width + x] ;
	}
	#endif	

   if (_miso == 0xff) return 0xffff;	// bail if not valid miso

	// First pass for other SPI busses use readRect to handle the read... 
	if (_spi_num != 0) {
		// Only SPI object has larger queue
		uint16_t colors;
		readRect(x, y, 1, 1, &colors);
		return colors;
	}

	uint8_t dummy __attribute__((unused));
	uint8_t r,g,b;

	beginSPITransaction(_SPI_CLOCK_READ);

	// Update our origin. 
	x+=_originx;
	y+=_originy;

	setAddr(x, y, x, y);
	writecommand_cont(HX8357_RAMRD); // read from RAM
	waitTransmitComplete();

	// Push 4 bytes over SPI
	_pkinetisk_spi->PUSHR = 0 | (pcs_data << 16) | SPI_PUSHR_CTAS(0)| SPI_PUSHR_CONT;
	waitFifoEmpty();    // wait for both queues to be empty.

	_pkinetisk_spi->PUSHR = 0 | (pcs_data << 16) | SPI_PUSHR_CTAS(0)| SPI_PUSHR_CONT;
	_pkinetisk_spi->PUSHR = 0 | (pcs_data << 16) | SPI_PUSHR_CTAS(0)| SPI_PUSHR_CONT;
	_pkinetisk_spi->PUSHR = 0 | (pcs_data << 16) | SPI_PUSHR_CTAS(0)| SPI_PUSHR_EOQ;

	// Wait for End of Queue
	while ((_pkinetisk_spi->SR & SPI_SR_EOQF) == 0) ;
	_pkinetisk_spi->SR = SPI_SR_EOQF;  // make sure it is clear

	// Read Pixel Data
	dummy = _pkinetisk_spi->POPR;	// Read a DUMMY byte of GRAM
	r = _pkinetisk_spi->POPR;		// Read a RED byte of GRAM
	g = _pkinetisk_spi->POPR;		// Read a GREEN byte of GRAM
	b = _pkinetisk_spi->POPR;		// Read a BLUE byte of GRAM

	endSPITransaction();
	return color565(r,g,b);
#else
	// Kinetisk
	uint16_t colors = 0;
	readRect(x, y, 1, 1, &colors);
	return colors;
#endif	
}

// Now lets see if we can read in multiple pixels
#ifdef KINETISK
void HX8357_t3n::readRect(int16_t x, int16_t y, int16_t w, int16_t h, uint16_t *pcolors)
{
	// Use our Origin. 
	x+=_originx;
	y+=_originy;
	//BUGBUG:: Should add some validation of X and Y

	#ifdef ENABLE_HX8357_FRAMEBUFFER
	if (_use_fbtft) {
		uint16_t * pfbPixel_row = &_pfbtft[ y*_width + x];
		for (;h>0; h--) {
			uint16_t * pfbPixel = pfbPixel_row;
			for (int i = 0 ;i < w; i++) {
				*pcolors++ = *pfbPixel++;
			}
			pfbPixel_row += _width;
		}
		return;	
	}
	#endif	

   if (_miso == 0xff) return;		// bail if not valid miso

	uint8_t rgb[3];               // RGB bytes received from the display
	uint8_t rgbIdx = 0;
	uint32_t txCount = w * h * 3; // number of bytes we will transmit to the display
	uint32_t rxCount = txCount;   // number of bytes we will receive back from the display

	beginSPITransaction(_SPI_CLOCK_READ);

	setAddr(x, y, x+w-1, y+h-1);
	writecommand_cont(HX8357_RAMRD); // read from RAM

	// transmit a DUMMY byte before the color bytes
	_pkinetisk_spi->PUSHR = 0 | (pcs_data << 16) | SPI_PUSHR_CTAS(0)| SPI_PUSHR_CONT;

	// skip values returned by the queued up transfers and the current in-flight transfer
	uint32_t sr = _pkinetisk_spi->SR;
	uint8_t skipCount = ((sr >> 4) & 0xF) + ((sr >> 12) & 0xF) + 1;

	while (txCount || rxCount) {
		// transmit another byte if possible
		if (txCount && (_pkinetisk_spi->SR & 0xF000) <= _fifo_full_test) {
			txCount--;
			if (txCount) {
				_pkinetisk_spi->PUSHR = READ_PIXEL_PUSH_BYTE | (pcs_data << 16) | SPI_PUSHR_CTAS(0)| SPI_PUSHR_CONT;
			} else {
				_pkinetisk_spi->PUSHR = READ_PIXEL_PUSH_BYTE | (pcs_data << 16) | SPI_PUSHR_CTAS(0)| SPI_PUSHR_EOQ;
			}
		}

		// receive another byte if possible, and either skip it or store the color
		if (rxCount && (_pkinetisk_spi->SR & 0xF0)) {
			rgb[rgbIdx] = _pkinetisk_spi->POPR;

			if (skipCount) {
				skipCount--;
			} else {
				rxCount--;
				rgbIdx++;
				if (rgbIdx == 3) {
					rgbIdx = 0;
					*pcolors++ = color565(rgb[0], rgb[1], rgb[2]);
				}
			}
		}
	}

	// wait for End of Queue
	while ((_pkinetisk_spi->SR & SPI_SR_EOQF) == 0) ;
	_pkinetisk_spi->SR = SPI_SR_EOQF;  // make sure it is clear
	endSPITransaction();

}
#elif defined(__IMXRT1052__) || defined(__IMXRT1062__)  // Teensy 4.x 
void HX8357_t3n::readRect(int16_t x, int16_t y, int16_t w, int16_t h, uint16_t *pcolors)
{
	// Use our Origin. 
	x+=_originx;
	y+=_originy;
	//BUGBUG:: Should add some validation of X and Y

	#ifdef ENABLE_HX8357_FRAMEBUFFER
	if (_use_fbtft) {
		uint16_t * pfbPixel_row = &_pfbtft[ y*_width + x];
		for (;h>0; h--) {
			uint16_t * pfbPixel = pfbPixel_row;
			for (int i = 0 ;i < w; i++) {
				*pcolors++ = *pfbPixel++;
			}
			pfbPixel_row += _width;
		}
		return;	
	}
	#endif	

   if (_miso == 0xff) return;		// bail if not valid miso

	uint8_t rgb[3];               // RGB bytes received from the display
	uint8_t rgbIdx = 0;
	uint32_t txCount = w * h * 3; // number of bytes we will transmit to the display
	uint32_t rxCount = txCount;   // number of bytes we will receive back from the display

	beginSPITransaction(_SPI_CLOCK_READ);

	setAddr(x, y, x+w-1, y+h-1);
	writecommand_cont(HX8357_RAMRD); // read from RAM


	// transmit a DUMMY byte before the color bytes
	writedata8_last(0);		// BUGBUG:: maybe fix this as this will wait until the byte fully transfers through.

	while (txCount || rxCount) {
		// transmit another byte if possible
		if (txCount && (_pimxrt_spi->SR & LPSPI_SR_TDF)) {
			txCount--;
			if (txCount) {
				_pimxrt_spi->TDR = 0;
			} else {
				maybeUpdateTCR(_tcr_dc_not_assert | LPSPI_TCR_FRAMESZ(7)); // remove the CONTINUE...
				while ((_pimxrt_spi->SR & LPSPI_SR_TDF) == 0) ;		// wait if queue was full
				_pimxrt_spi->TDR = 0;
			}
		}

		// receive another byte if possible, and either skip it or store the color
		if (rxCount && !(_pimxrt_spi->RSR & LPSPI_RSR_RXEMPTY)) {
			rgb[rgbIdx] = _pimxrt_spi->RDR;

			rxCount--;
			rgbIdx++;
			if (rgbIdx == 3) {
				rgbIdx = 0;
				*pcolors++ = color565(rgb[0], rgb[1], rgb[2]);
			}
		}
	}

	// We should have received everything so should be done
	endSPITransaction();
}

#else

// Teensy LC version
void HX8357_t3n::readRect(int16_t x, int16_t y, int16_t w, int16_t h, uint16_t *pcolors)
{
	// Use our Origin. 
	x+=_originx;
	y+=_originy;
	//BUGBUG:: Should add some validation of X and Y

   if (_miso == 0xff) return;		// bail if not valid miso

	uint8_t rgb[3];               // RGB bytes received from the display
	uint8_t rgbIdx = 0;
	uint32_t txCount = w * h * 3; // number of bytes we will transmit to the display
	uint32_t rxCount = txCount;   // number of bytes we will receive back from the display

	beginSPITransaction(_SPI_CLOCK_READ);

	setAddr(x, y, x+w-1, y+h-1);
	writecommand_cont(HX8357_RAMRD); // read from RAM

	// transmit a DUMMY byte before the color bytes
	writedata8_cont(0);

	// Wait until that one returns, Could do a little better and double buffer but this is easer for now.
	waitTransmitComplete();

	// Since double buffer setup lets try keeping read/write in sync
#define RRECT_TIMEOUT 0xffff	
#undef 	READ_PIXEL_PUSH_BYTE
#define READ_PIXEL_PUSH_BYTE 0 // try with zero to see... 	
	uint16_t timeout_countdown = RRECT_TIMEOUT;
	uint16_t dl_in;
	// Write out first byte:

	while (!(_pkinetisl_spi->S & SPI_S_SPTEF)) ; // Not worried that this can completely hang?
	_pkinetisl_spi->DL = READ_PIXEL_PUSH_BYTE;

	while (rxCount && timeout_countdown) {
		// Now wait until we can output something
		dl_in = 0xffff;
		if (rxCount > 1) {
			while (!(_pkinetisl_spi->S & SPI_S_SPTEF)) ; // Not worried that this can completely hang?
			if (_pkinetisl_spi->S & SPI_S_SPRF)
				dl_in = _pkinetisl_spi->DL;  
			_pkinetisl_spi->DL = READ_PIXEL_PUSH_BYTE;
		}

		// Now wait until there is a byte available to receive
		while ((dl_in != 0xffff) && !(_pkinetisl_spi->S & SPI_S_SPRF) && --timeout_countdown) ;
		if (timeout_countdown) {   // Make sure we did not get here because of timeout 
			rxCount--;
			rgb[rgbIdx] = (dl_in != 0xffff)? dl_in : _pkinetisl_spi->DL;
			rgbIdx++;
			if (rgbIdx == 3) {
				rgbIdx = 0;
				*pcolors++ = color565(rgb[0], rgb[1], rgb[2]);
			}
			timeout_countdown = timeout_countdown;
		}
	}

	// Debug code. 
/*	if (timeout_countdown == 0) {
		Serial.print("RRect Timeout ");
		Serial.println(rxCount, DEC);
	} */
	endSPITransaction();
}
#endif		

// Now lets see if we can writemultiple pixels
void HX8357_t3n::writeRect(int16_t x, int16_t y, int16_t w, int16_t h, const uint16_t *pcolors)
{

	if (x == CENTER) x = (_width - w) / 2;
	if (y == CENTER) y = (_height - h) / 2;
	x+=_originx;
	y+=_originy;
	uint16_t x_clip_left = 0;  // How many entries at start of colors to skip at start of row
	uint16_t x_clip_right = 0;    // how many color entries to skip at end of row for clipping
	// Rectangular clipping 

	// See if the whole thing out of bounds...
	if((x >= _displayclipx2) || (y >= _displayclipy2)) return;
	if (((x+w) <= _displayclipx1) || ((y+h) <= _displayclipy1)) return;

	// In these cases you can not do simple clipping, as we need to synchronize the colors array with the
	// We can clip the height as when we get to the last visible we don't have to go any farther. 
	// also maybe starting y as we will advance the color array. 
 	if(y < _displayclipy1) {
 		int dy = (_displayclipy1 - y);
 		h -= dy; 
 		pcolors += (dy*w); // Advance color array to 
 		y = _displayclipy1; 	
 	}

	if((y + h - 1) >= _displayclipy2) h = _displayclipy2 - y;

	// For X see how many items in color array to skip at start of row and likewise end of row 
	if(x < _displayclipx1) {
		x_clip_left = _displayclipx1-x; 
		w -= x_clip_left; 
		x = _displayclipx1; 	
	}
	if((x + w - 1) >= _displayclipx2) {
		x_clip_right = w;
		w = _displayclipx2  - x;
		x_clip_right -= w; 
	} 

	#ifdef ENABLE_HX8357_FRAMEBUFFER
	if (_use_fbtft) {
		updateChangedRange(x, y, w, h);		// update the range of the screen that has been changed;
		uint16_t * pfbPixel_row = &_pfbtft[ y*_width + x];
		for (;h>0; h--) {
			uint16_t * pfbPixel = pfbPixel_row;
			pcolors += x_clip_left;
			for (int i = 0 ;i < w; i++) {
				*pfbPixel++ = *pcolors++;
			}
			pfbPixel_row += _width;
			pcolors += x_clip_right;

		}
		return;	
	}
	#endif

   	beginSPITransaction(_SPI_CLOCK);
	setAddr(x, y, x+w-1, y+h-1);
	writecommand_cont(HX8357_RAMWR);
	for(y=h; y>0; y--) {
		pcolors += x_clip_left;
		for(x=w; x>1; x--) {
			writedata16_cont(*pcolors++);
		}
		writedata16_last(*pcolors++);
		pcolors += x_clip_right;
	}
	endSPITransaction();
}

// writeRect8BPP - 	write 8 bit per pixel paletted bitmap
//					bitmap data in array at pixels, one byte per pixel
//					color palette data in array at palette
void HX8357_t3n::writeRect8BPP(int16_t x, int16_t y, int16_t w, int16_t h, const uint8_t *pixels, const uint16_t * palette )
{
	//Serial.printf("\nWR8: %d %d %d %d %x\n", x, y, w, h, (uint32_t)pixels);
	x+=_originx;
	y+=_originy;

	uint16_t x_clip_left = 0;  // How many entries at start of colors to skip at start of row
	uint16_t x_clip_right = 0;    // how many color entries to skip at end of row for clipping
	// Rectangular clipping 

	// See if the whole thing out of bounds...
	if((x >= _displayclipx2) || (y >= _displayclipy2)) return;
	if (((x+w) <= _displayclipx1) || ((y+h) <= _displayclipy1)) return;

	// In these cases you can not do simple clipping, as we need to synchronize the colors array with the
	// We can clip the height as when we get to the last visible we don't have to go any farther. 
	// also maybe starting y as we will advance the color array. 
 	if(y < _displayclipy1) {
 		int dy = (_displayclipy1 - y);
 		h -= dy; 
 		pixels += (dy*w); // Advance color array to 
 		y = _displayclipy1; 	
 	}

	if((y + h - 1) >= _displayclipy2) h = _displayclipy2 - y;

	// For X see how many items in color array to skip at start of row and likewise end of row 
	if(x < _displayclipx1) {
		x_clip_left = _displayclipx1-x; 
		w -= x_clip_left; 
		x = _displayclipx1; 	
	}
	if((x + w - 1) >= _displayclipx2) {
		x_clip_right = w;
		w = _displayclipx2  - x;
		x_clip_right -= w; 
	} 
	//Serial.printf("WR8C: %d %d %d %d %x- %d %d\n", x, y, w, h, (uint32_t)pixels, x_clip_right, x_clip_left);
	#ifdef ENABLE_HX8357_FRAMEBUFFER
	if (_use_fbtft) {
		updateChangedRange(x, y, w, h);		// update the range of the screen that has been changed;
		uint16_t * pfbPixel_row = &_pfbtft[ y*_width + x];
		for (;h>0; h--) {
			pixels += x_clip_left;
			uint16_t * pfbPixel = pfbPixel_row;
			for (int i = 0 ;i < w; i++) {
				*pfbPixel++ = palette[*pixels++];
			}
			pixels += x_clip_right;
			pfbPixel_row += _width;
		}
		return;	
	}
	#endif

	beginSPITransaction(_SPI_CLOCK);
	setAddr(x, y, x+w-1, y+h-1);
	writecommand_cont(HX8357_RAMWR);
	for(y=h; y>0; y--) {
		pixels += x_clip_left;
		//Serial.printf("%x: ", (uint32_t)pixels);
		for(x=w; x>1; x--) {
			//Serial.print(*pixels, DEC);
			writedata16_cont(palette[*pixels++]);
		}
		//Serial.println(*pixels, DEC);
		writedata16_last(palette[*pixels++]);
		pixels += x_clip_right;
	}
	endSPITransaction();
}

// writeRect4BPP - 	write 4 bit per pixel paletted bitmap
//					bitmap data in array at pixels, 4 bits per pixel
//					color palette data in array at palette
//					width must be at least 2 pixels
void HX8357_t3n::writeRect4BPP(int16_t x, int16_t y, int16_t w, int16_t h, const uint8_t *pixels, const uint16_t * palette )
{
	// Simply call through our helper
	writeRectNBPP(x, y, w, h,  4, pixels, palette );
}

// writeRect2BPP - 	write 2 bit per pixel paletted bitmap
//					bitmap data in array at pixels, 4 bits per pixel
//					color palette data in array at palette
//					width must be at least 4 pixels
void HX8357_t3n::writeRect2BPP(int16_t x, int16_t y, int16_t w, int16_t h, const uint8_t *pixels, const uint16_t * palette )
{
	// Simply call through our helper
	writeRectNBPP(x, y, w, h,  2, pixels, palette );

}

///============================================================================
// writeRect1BPP - 	write 1 bit per pixel paletted bitmap
//					bitmap data in array at pixels, 4 bits per pixel
//					color palette data in array at palette
//					width must be at least 8 pixels
void HX8357_t3n::writeRect1BPP(int16_t x, int16_t y, int16_t w, int16_t h, const uint8_t *pixels, const uint16_t * palette )
{
	// Simply call through our helper
	writeRectNBPP(x, y, w, h,  1, pixels, palette );
}



///============================================================================
// writeRectNBPP - 	write N(1, 2, 4, 8) bit per pixel paletted bitmap
//					bitmap data in array at pixels
//  Currently writeRect1BPP, writeRect2BPP, writeRect4BPP use this to do all of the work. 
void HX8357_t3n::writeRectNBPP(int16_t x, int16_t y, int16_t w, int16_t h,  uint8_t bits_per_pixel, 
		const uint8_t *pixels, const uint16_t * palette )
{
	//Serial.printf("\nWR8: %d %d %d %d %x\n", x, y, w, h, (uint32_t)pixels);
	x+=_originx;
	y+=_originy;
	uint8_t pixels_per_byte = 8/ bits_per_pixel;
	uint16_t count_of_bytes_per_row = (w + pixels_per_byte -1)/pixels_per_byte;		// Round up to handle non multiples
	uint8_t row_shift_init = 8 - bits_per_pixel;				// We shift down 6 bits by default 
	uint8_t pixel_bit_mask = (1 << bits_per_pixel) - 1; 		// get mask to use below
	// Rectangular clipping 

	// See if the whole thing out of bounds...
	if((x >= _displayclipx2) || (y >= _displayclipy2)) return;
	if (((x+w) <= _displayclipx1) || ((y+h) <= _displayclipy1)) return;

	// In these cases you can not do simple clipping, as we need to synchronize the colors array with the
	// We can clip the height as when we get to the last visible we don't have to go any farther. 
	// also maybe starting y as we will advance the color array. 
	// Again assume multiple of 8 for width
 	if(y < _displayclipy1) {
 		int dy = (_displayclipy1 - y);
 		h -= dy; 
 		pixels += dy * count_of_bytes_per_row;
 		y = _displayclipy1; 	
 	}

	if((y + h - 1) >= _displayclipy2) h = _displayclipy2 - y;

	// For X see how many items in color array to skip at start of row and likewise end of row 
	if(x < _displayclipx1) {
		uint16_t x_clip_left = _displayclipx1-x; 
		w -= x_clip_left; 
		x = _displayclipx1; 
		// Now lets update pixels to the rigth offset and mask
		uint8_t x_clip_left_bytes_incr = x_clip_left / pixels_per_byte;
		pixels += x_clip_left_bytes_incr;
		row_shift_init = 8 - (x_clip_left - (x_clip_left_bytes_incr * pixels_per_byte) + 1) * bits_per_pixel; 	
	}

	if((x + w - 1) >= _displayclipx2) {
		w = _displayclipx2  - x;
	} 

	const uint8_t * pixels_row_start = pixels;  // remember our starting position offset into row

	#ifdef ENABLE_HX8357_FRAMEBUFFER
	if (_use_fbtft) {
		updateChangedRange(x, y, w, h);		// update the range of the screen that has been changed;
		uint16_t * pfbPixel_row = &_pfbtft[ y*_width + x];
		for (;h>0; h--) {
			uint16_t * pfbPixel = pfbPixel_row;
			pixels = pixels_row_start;				// setup for this row
			uint8_t pixel_shift = row_shift_init;			// Setup mask

			for (int i = 0 ; i < w; i++) {
				*pfbPixel++ = palette[((*pixels)>>pixel_shift) & pixel_bit_mask];
				if (!pixel_shift) {
					pixel_shift = 8 - bits_per_pixel;	//setup next mask
					pixels++;
				} else {
					pixel_shift -= bits_per_pixel;
				}
			}
			pfbPixel_row += _width;
			pixels_row_start += count_of_bytes_per_row;
		}
		return;	

	}
	#endif

	beginSPITransaction(_SPI_CLOCK);
	setAddr(x, y, x+w-1, y+h-1);
	writecommand_cont(HX8357_RAMWR);
	for (;h>0; h--) {
		pixels = pixels_row_start;				// setup for this row
		uint8_t pixel_shift = row_shift_init;			// Setup mask

		for (int i = 0 ;i < w; i++) {
			writedata16_cont(palette[((*pixels)>>pixel_shift) & pixel_bit_mask]);
			if (!pixel_shift) {
				pixel_shift = 8 - bits_per_pixel;	//setup next mask
				pixels++;
			} else {
				pixel_shift -= bits_per_pixel;
			}
		}
		pixels_row_start += count_of_bytes_per_row;
	}
	writecommand_last(HX8357_NOP);
	endSPITransaction();
}

static const uint8_t init_commands[] = {
	1, HX8357_SWRESET,
	0x80, 100/5,		// delay 100ms
	4, HX8357D_SETC, 0xFF, 0x83, 0x57,
	0x80, 500/5,		// delay 500ms
	5, HX8357_SETRGB, 0x80, 0x00, 0X06, 0X06, // enable SDO pin
	2, HX8357D_SETCOM, 0x25, 			   // -1.52V
	2, HX8357_SETOSC, 0x68,				   // Normal mode 70Hz, Idle mode 55 Hz
	2, HX8357_SETPANEL, 0x05,			   // BGR, Gate direction swapped
	7, HX8357_SETPWR1, 0x00, 0x15, 0x1C, 0x1C, 0x83, 0xAA,
	7, HX8357D_SETSTBA, 0x50, 0x50, 0x01, 0x3C, 0x1E, 0x08,
	8, HX8357D_SETCYC, 0x02, 0x40, 0x00, 0x2A, 0x2A, 0x0D, 0x78,
	35, HX8357D_SETGAMMA, 0x02, 0x0A, 0x11, 0x1d, 0x23, 0x35, 0x41, 
	                      0x4b, 0x4b, 0x42, 0x3A, 0x27, 0x1B, 0x08, 
	                      0x09, 0x03, 0x02, 0x0A, 0x11, 0x1d, 0x23, 
	                      0x35, 0x41, 0x4b, 0x4b, 0x42, 0x3A, 0x27, 
	                      0x1B, 0x08, 0x09, 0x03, 0x00, 0x01, // Gamma curve selected
	2, HX8357_COLMOD, 0x55, //16 bit format
	2, HX8357_MADCTL, 0xC0, // Memory Access Control
	2, HX8357_TEON, 0x00,
	3, HX8357_TEARLINE, 0x00, 0x02,
	1, HX8357_SLPOUT,
    0x80, 150 / 5, // Exit Sleep, then delay 150 ms
    1, HX8357_DISPON,
    0x80, 50 / 5, // Main screen turn on, delay 50 ms
        0,             // END OF COMMAND LIST
};

  
void HX8357_t3n::begin(uint32_t spi_clock, uint32_t spi_clock_read)
{
    // verify SPI pins are valid;
	// allow user to say use current ones...
	_SPI_CLOCK = spi_clock;				// #define HX8357_SPICLOCK 30000000
	_SPI_CLOCK_READ = spi_clock_read; 	//#define HX8357_SPICLOCK_READ 2000000

	Serial.printf("_t3n::begin mosi:%d miso:%d SCLK:%d CS:%d DC:%d SPI clocks: %lu %lu\n", _mosi, _miso, _sclk, _cs, _dc, _SPI_CLOCK, _SPI_CLOCK_READ); Serial.flush();

	if (SPI.pinIsMOSI(_mosi) && ((_miso == 0xff) || SPI.pinIsMISO(_miso)) && SPI.pinIsSCK(_sclk)) {
		_pspi = &SPI;
		_spi_num = 0;          // Which buss is this spi on? 
		#ifdef KINETISK
		_pkinetisk_spi = &KINETISK_SPI0;  // Could hack our way to grab this from SPI object, but...
		_fifo_full_test = (3 << 12);
		#elif defined(__IMXRT1052__) || defined(__IMXRT1062__)  // Teensy 4.x 
		_pimxrt_spi = &IMXRT_LPSPI4_S;  // Could hack our way to grab this from SPI object, but...
	#else
		_pkinetisl_spi = &KINETISL_SPI0;
		#endif				
	
	#if defined(__MK64FX512__) || defined(__MK66FX1M0__) || defined(__IMXRT1062__) || defined(__MKL26Z64__)
	} else if (SPI1.pinIsMOSI(_mosi) && ((_miso == 0xff) || SPI1.pinIsMISO(_miso)) && SPI1.pinIsSCK(_sclk)) {
		_pspi = &SPI1;
		_spi_num = 1;          // Which buss is this spi on? 
		#ifdef KINETISK
		_pkinetisk_spi = &KINETISK_SPI1;  // Could hack our way to grab this from SPI object, but...
		_fifo_full_test = (0 << 12);
		#elif defined(__IMXRT1052__) || defined(__IMXRT1062__)  // Teensy 4.x 
		_pimxrt_spi = &IMXRT_LPSPI3_S;  // Could hack our way to grab this from SPI object, but...
		#else
		_pkinetisl_spi = &KINETISL_SPI1;
		#endif				
	#if !defined(__MKL26Z64__)
	} else if (SPI2.pinIsMOSI(_mosi) && ((_miso == 0xff) || SPI2.pinIsMISO(_miso)) && SPI2.pinIsSCK(_sclk)) {
		_pspi = &SPI2;
		_spi_num = 2;          // Which buss is this spi on? 
		#ifdef KINETISK
		_pkinetisk_spi = &KINETISK_SPI2;  // Could hack our way to grab this from SPI object, but...
		_fifo_full_test = (0 << 12);
		#elif defined(__IMXRT1052__) || defined(__IMXRT1062__)  // Teensy 4.x 
		_pimxrt_spi = &IMXRT_LPSPI1_S;  // Could hack our way to grab this from SPI object, but...
		#endif				
	#endif
	#endif
	} else {
		Serial.println("HX8357_t3n: The IO pins on the constructor are not valid SPI pins");
	
		Serial.printf("    mosi:%d miso:%d SCLK:%d CS:%d DC:%d\n", _mosi, _miso, _sclk, _cs, _dc); Serial.flush();
		return;  // most likely will go bomb

	}
	// Make sure we have all of the proper SPI pins selected.
	_pspi->setMOSI(_mosi);
	_pspi->setSCK(_sclk);
	if (_miso != 0xff) _pspi->setMISO(_miso);

	// Hack to get hold of the SPI Hardware information... 
 	uint32_t *pa = (uint32_t*)((void*)_pspi);
	_spi_hardware = (SPIClass::SPI_Hardware_t*)(void*)pa[1];

	_pspi->begin();
#ifdef KINETISK
	if (_pspi->pinIsChipSelect(_cs, _dc)) {
		pcs_data = _pspi->setCS(_cs);
		pcs_command = pcs_data | _pspi->setCS(_dc);
	} else {
		// See if at least DC is on chipselect pin, if so try to limp along...
		if (_pspi->pinIsChipSelect(_dc)) {
			pcs_data = 0;
			pcs_command = pcs_data | _pspi->setCS(_dc);
			pinMode(_cs, OUTPUT);
			_csport    = portOutputRegister(digitalPinToPort(_cs));
			_cspinmask = digitalPinToBitMask(_cs);
			*_csport |= _cspinmask;
		} else {
			pcs_data = 0;
			pcs_command = 0;
  			Serial.println("HX8357_t3n: Error not DC is not valid hardware CS pin");
			return;
		}
	}
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
